akkoyun/B101/Output/2026-02-18/Schematic Print/Schematic Prints.PDF

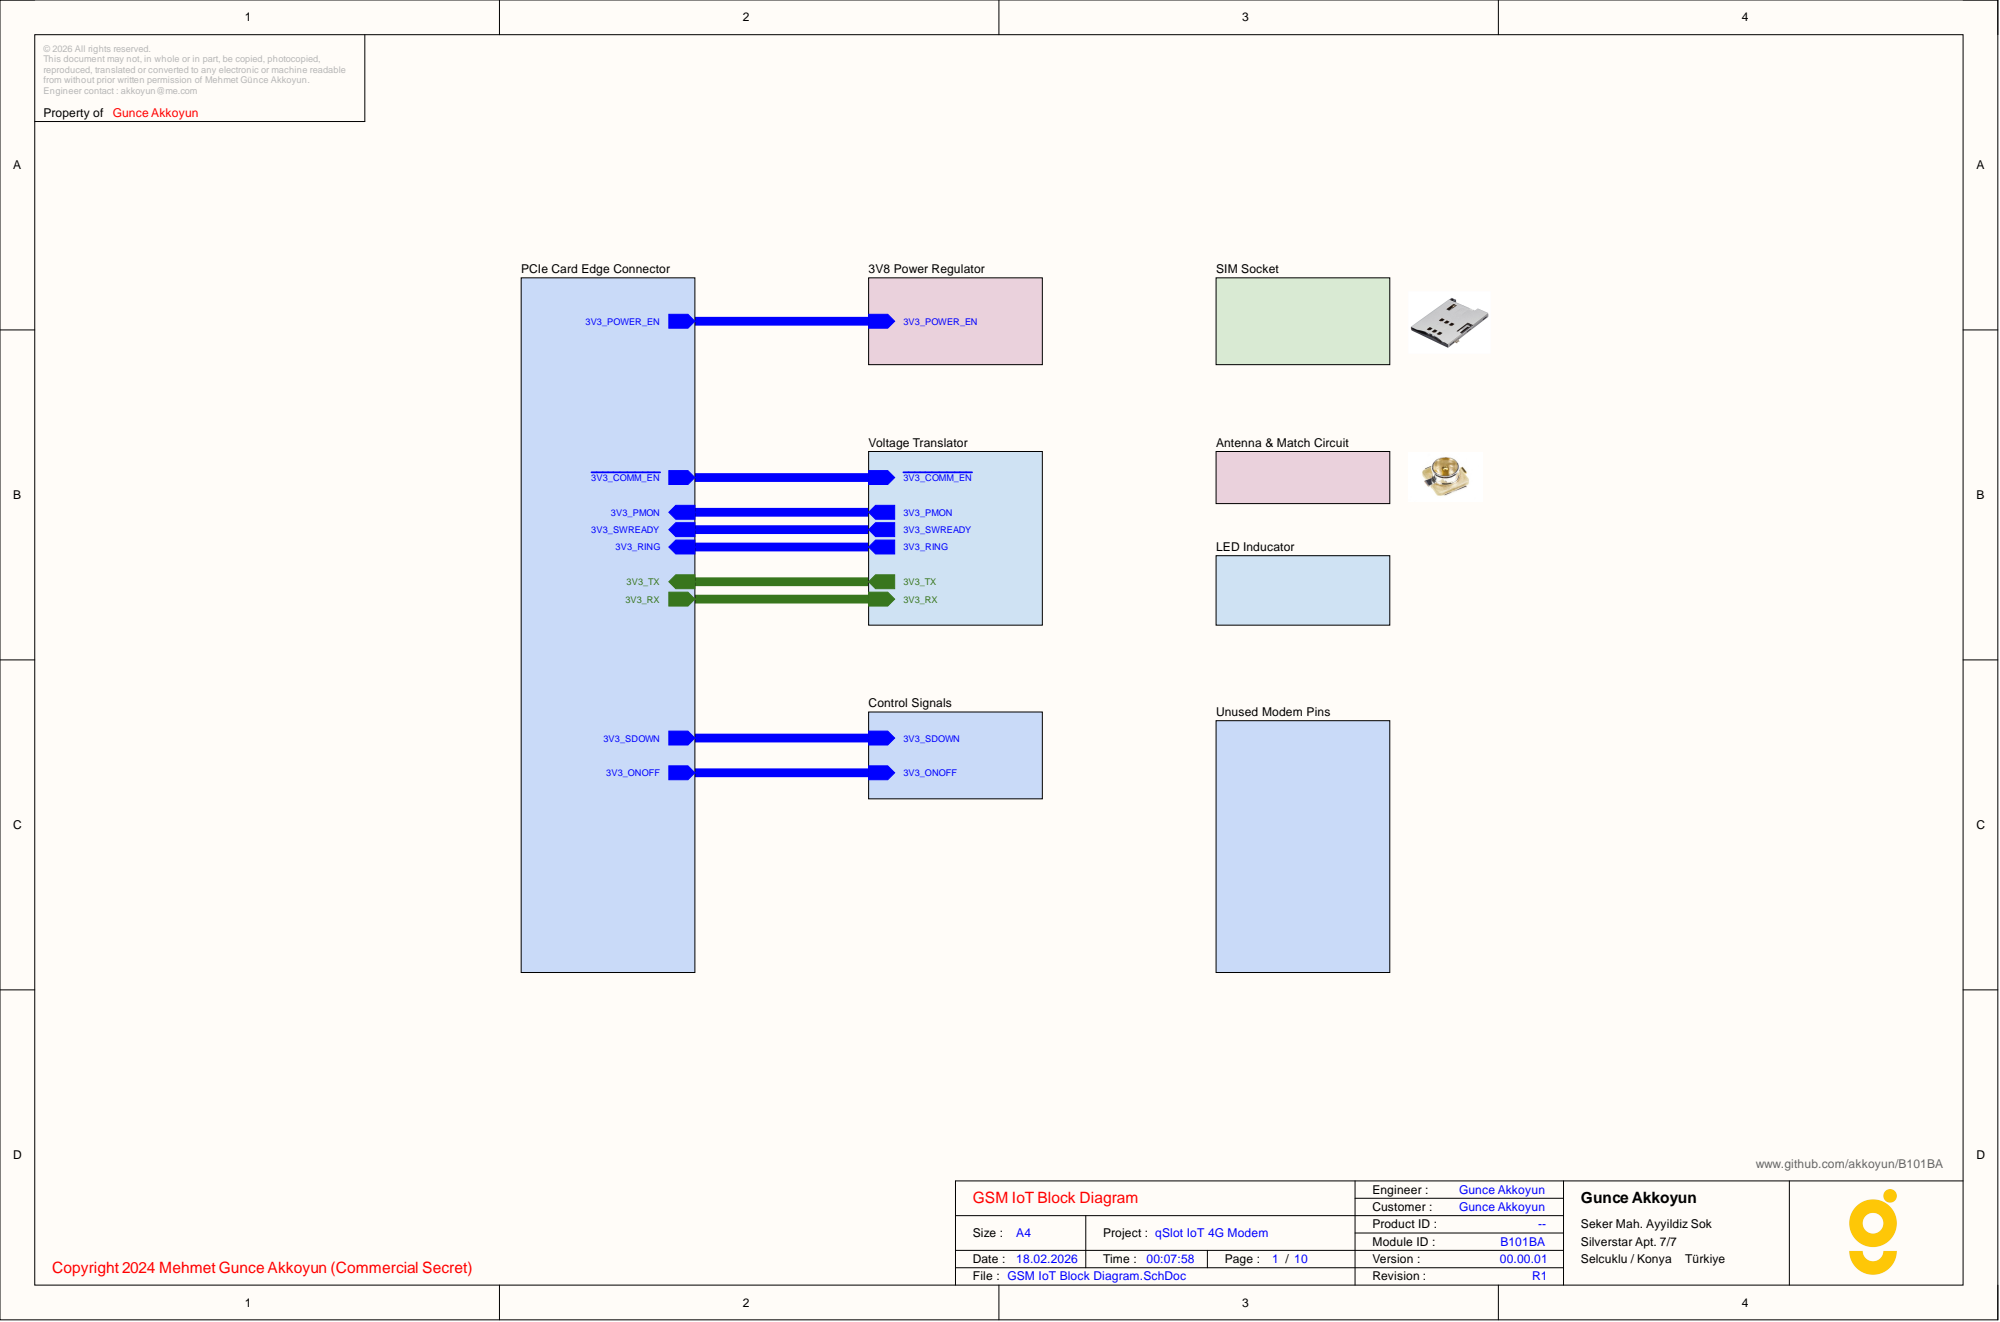
[picture p13: page 1]

© 2026 All rights reserved.
This document may not, in whole or in part, be copied, photocopied,
reproduced, translated or converted to any electronic or machine readable
from without prior written permission of Mehmet Günce Akkoyun.
Engineer contact : akkoyun@me.com

Property of Gunce Akkoyun

PCIe Card Edge Connector

www.github.com/akkoyun/B101BA

GSM IoT Block Diagram

Seker Mah. Ayyildiz Sok
Silverstar Apt. 7/7
Selcuklu / Konya Türkiye

Copyright 2024 Mehmet Gunce Akkoyun (Commercial Secret)

File : GSM IoT Block Diagram.SchDoc

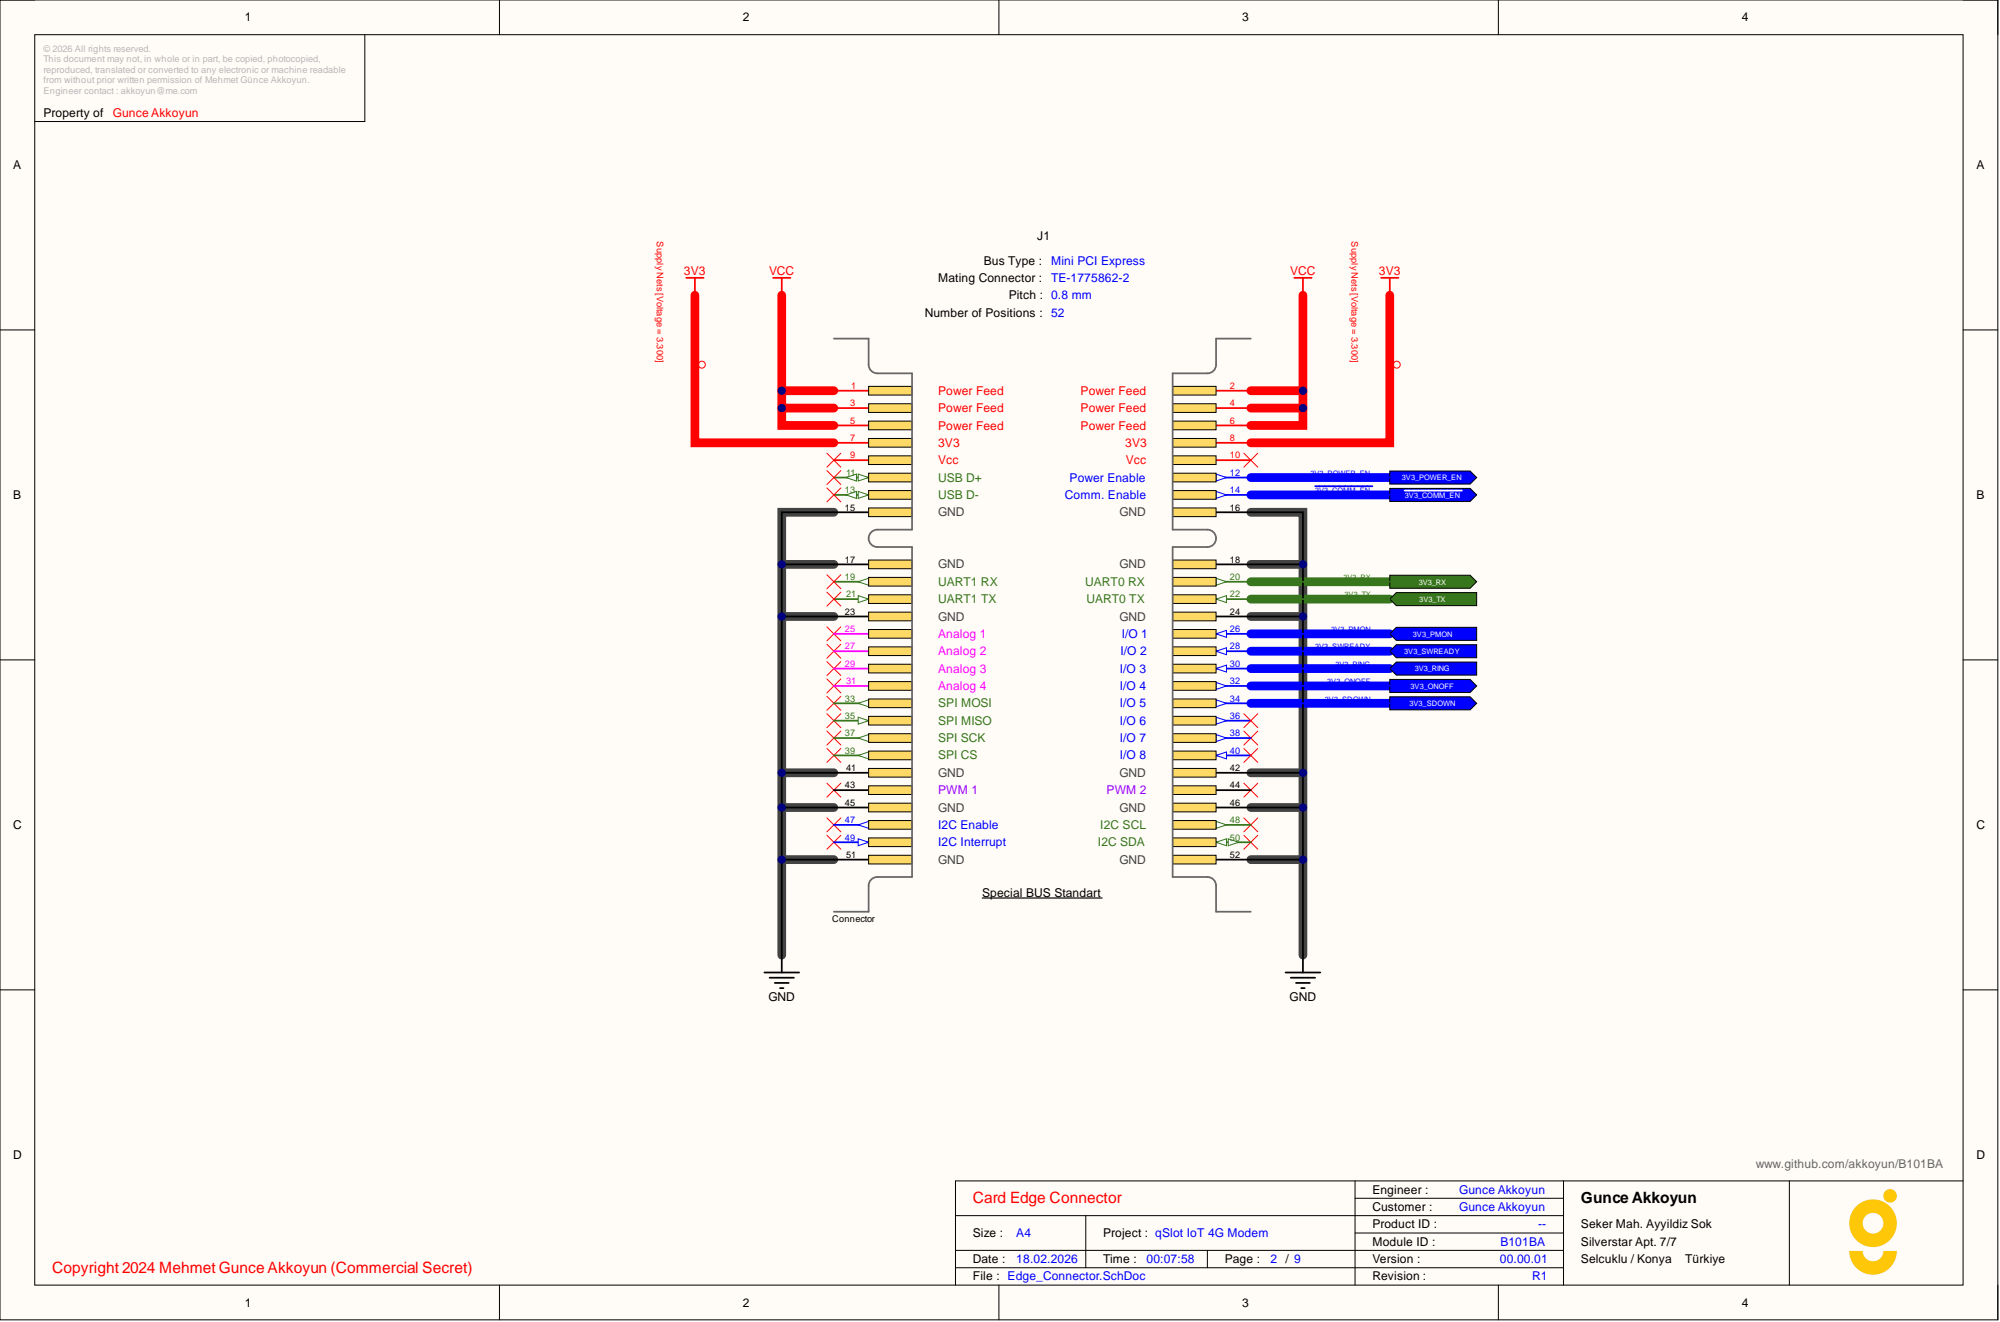
[picture p14: page 2]

Property of Gunce Akkoyun

www.github.com/akkoyun/B101BA

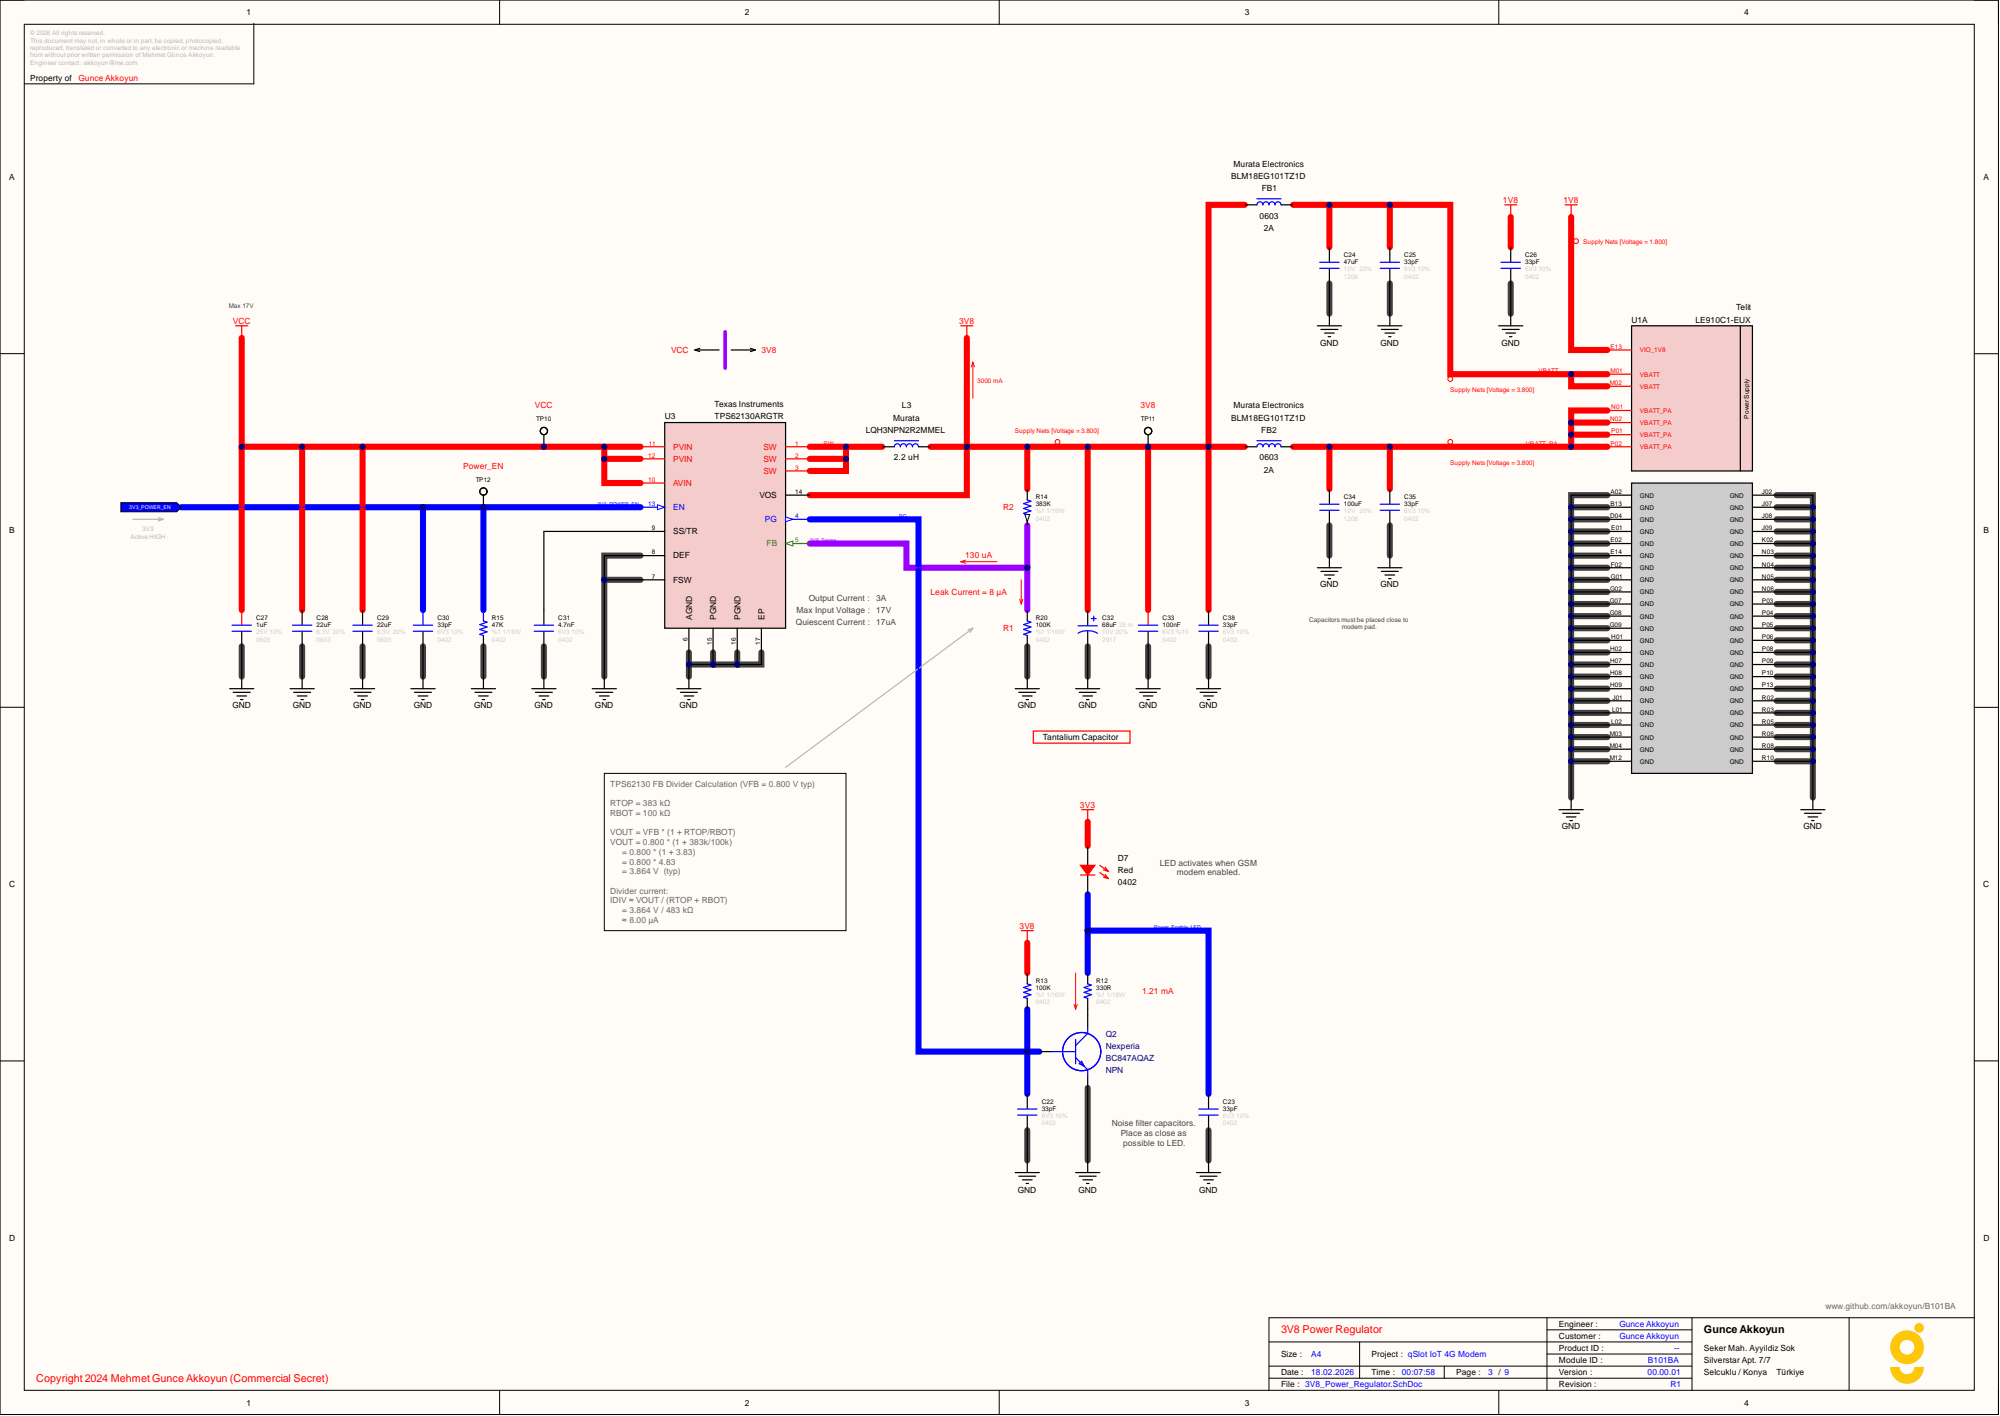
[picture p15: page 3]

Property of Gunce Akkoyun

Capacitors must be placed close to

TPS62130 FB Divider Calculation (VFB = 0.800 V typ)

Divider current:
IDIV ≈ VOUT / (RTOP + RBOT)

Noise filter capacitors.
Place as close as
possible to LED.

www.github.com/akkoyun/B101BA

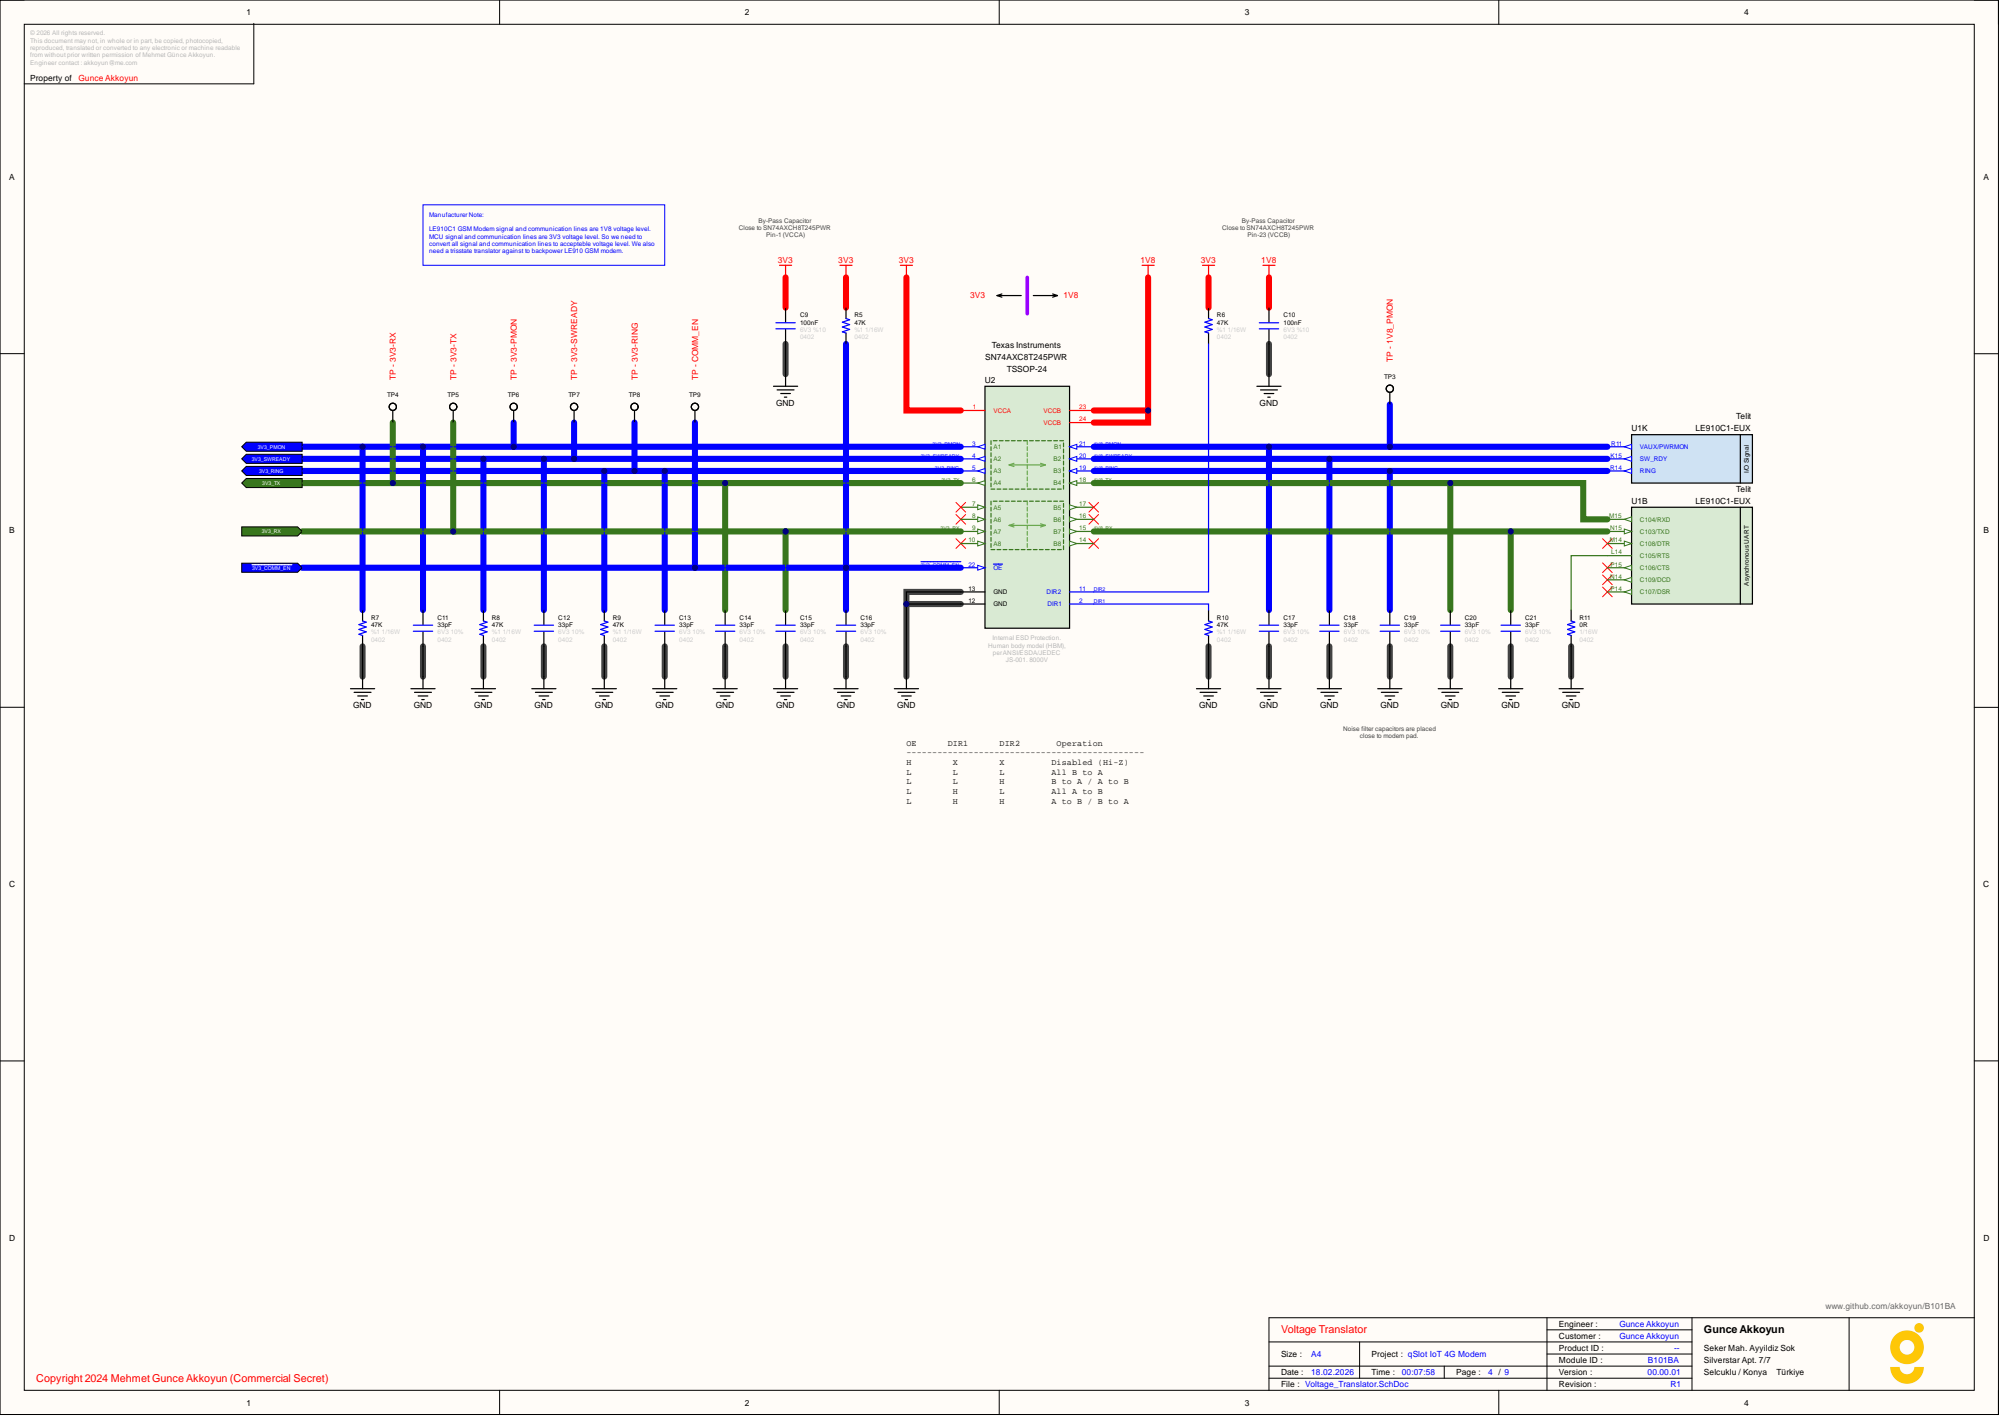
[picture p16: page 4]

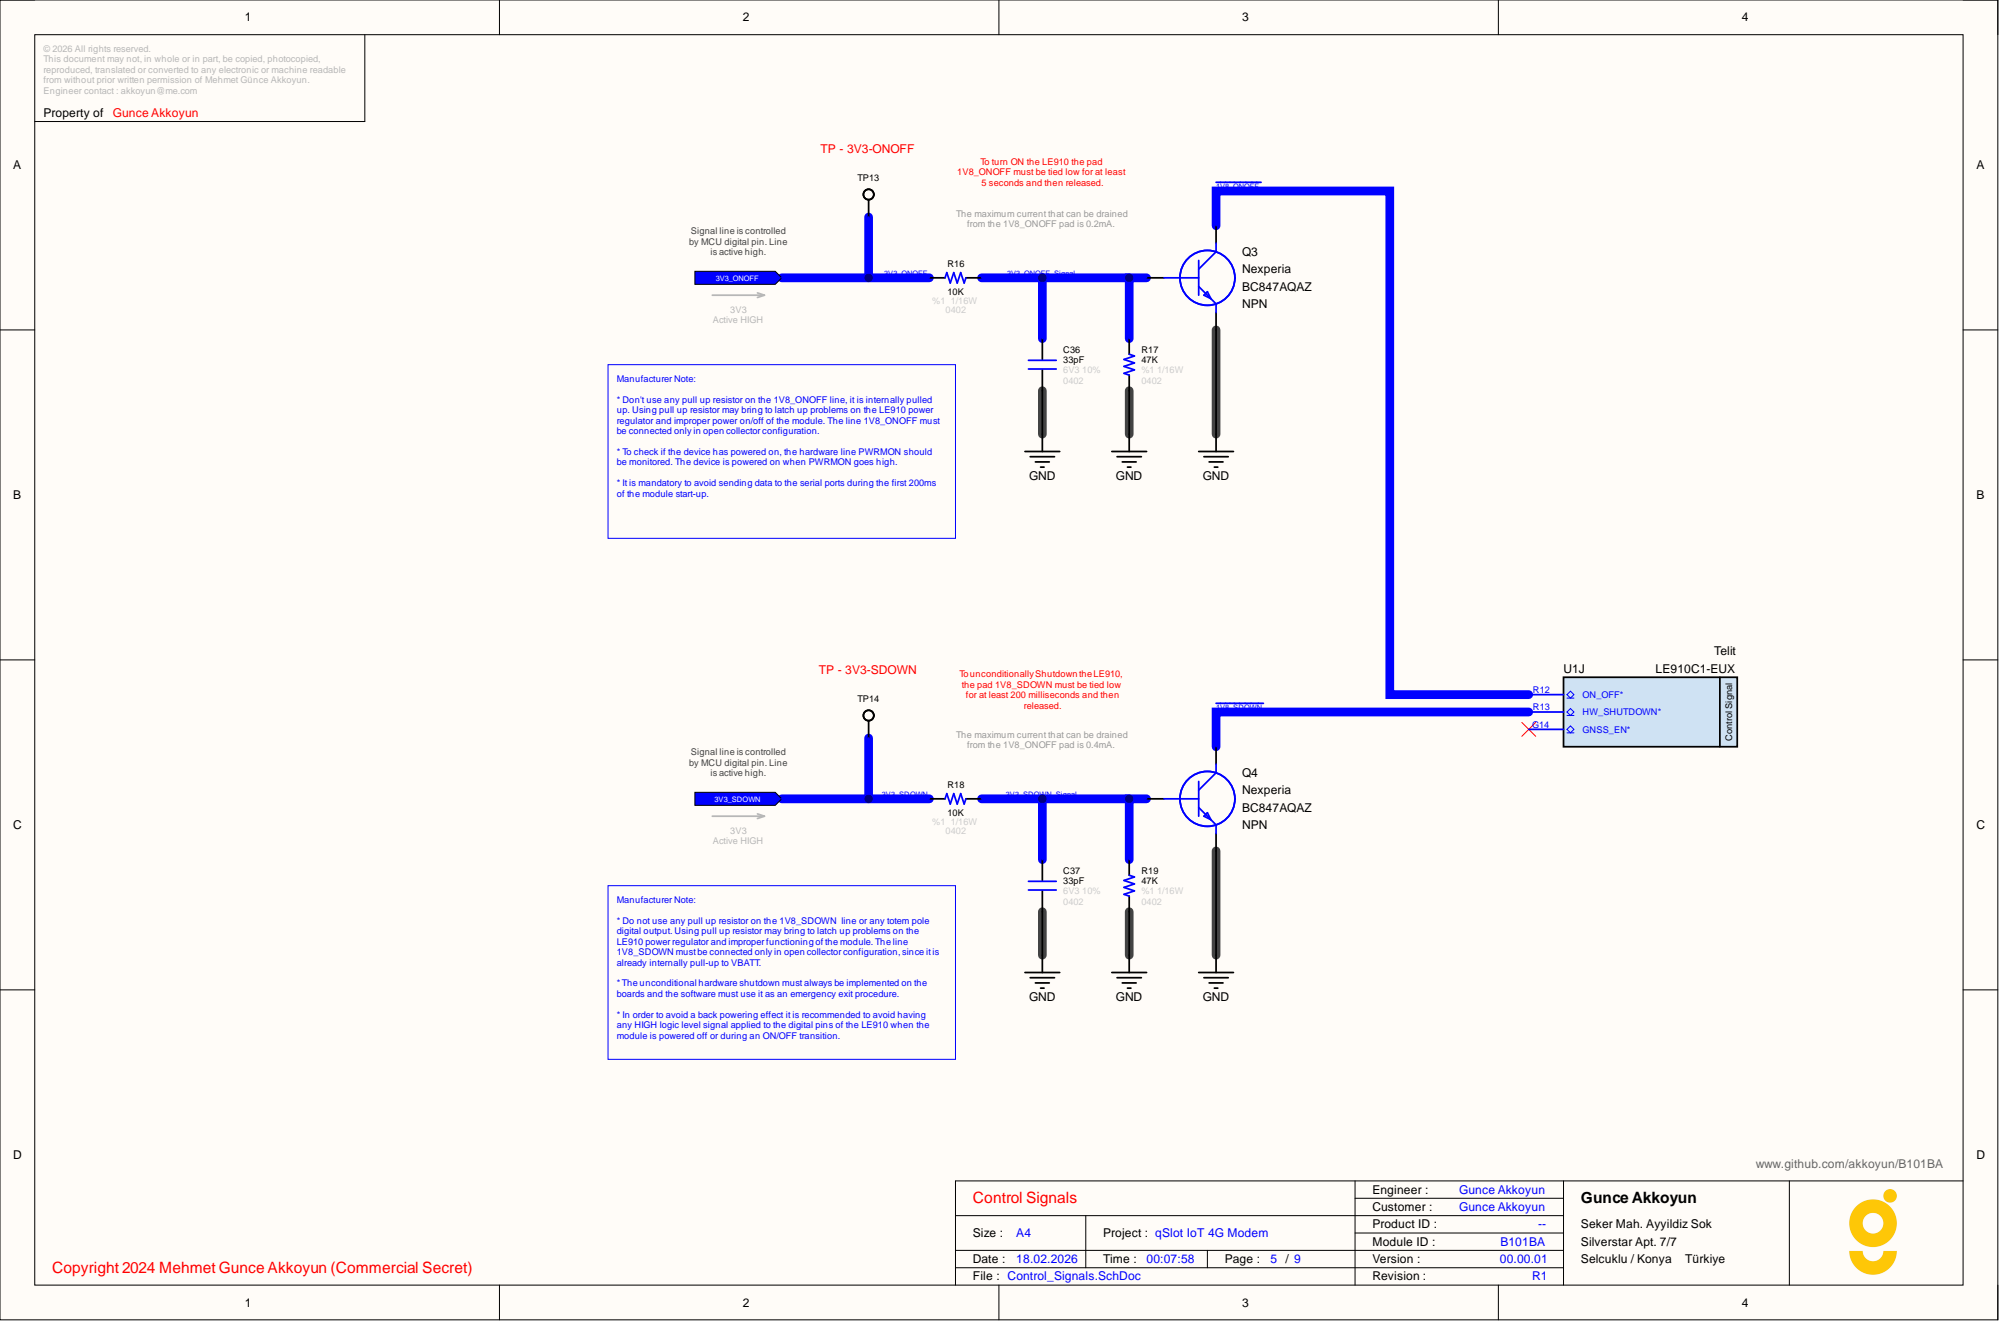
[picture p17: page 5]

Property of Gunce Akkoyun

To turn ON the LE910 the pad
1V8_ONOFF must be tied low for at least
5 seconds and then released.

The maximum current that can be drained
from the 1V8_ONOFF pad is 0.2mA.

Signal line is controlled
by MCU digital pin. Line
is active high.

* Don't use any pull up resistor on the 1V8_ONOFF line, it is internally pulled
up. Using pull up resistor may bring to latch up problems on the LE910 power
regulator and improper power on/off of the module. The line 1V8_ONOFF must
be connected only in open collector configuration.

* To check if the device has powered on, the hardware line PWRMON should
be monitored. The device is powered on when PWRMON goes high.

* It is mandatory to avoid sending data to the serial ports during the first 200ms
of the module start-up.

To unconditionally Shutdown the LE910,
the pad 1V8_SDOWN must be tied low
for at least 200 milliseconds and then

from the 1V8_ONOFF pad is 0.4mA.

* Do not use any pull up resistor on the 1V8_SDOWN line or any totem pole
digital output. Using pull up resistor may bring to latch up problems on the
LE910 power regulator and improper functioning of the module. The line
1V8_SDOWN must be connected only in open collector configuration, since it is
already internally pull-up to VBATT.

* The unconditional hardware shutdown must always be implemented on the
boards and the software must use it as an emergency exit procedure.

* In order to avoid a back powering effect it is recommended to avoid having
any HIGH logic level signal applied to the digital pins of the LE910 when the
module is powered off or during an ON/OFF transition.

www.github.com/akkoyun/B101BA

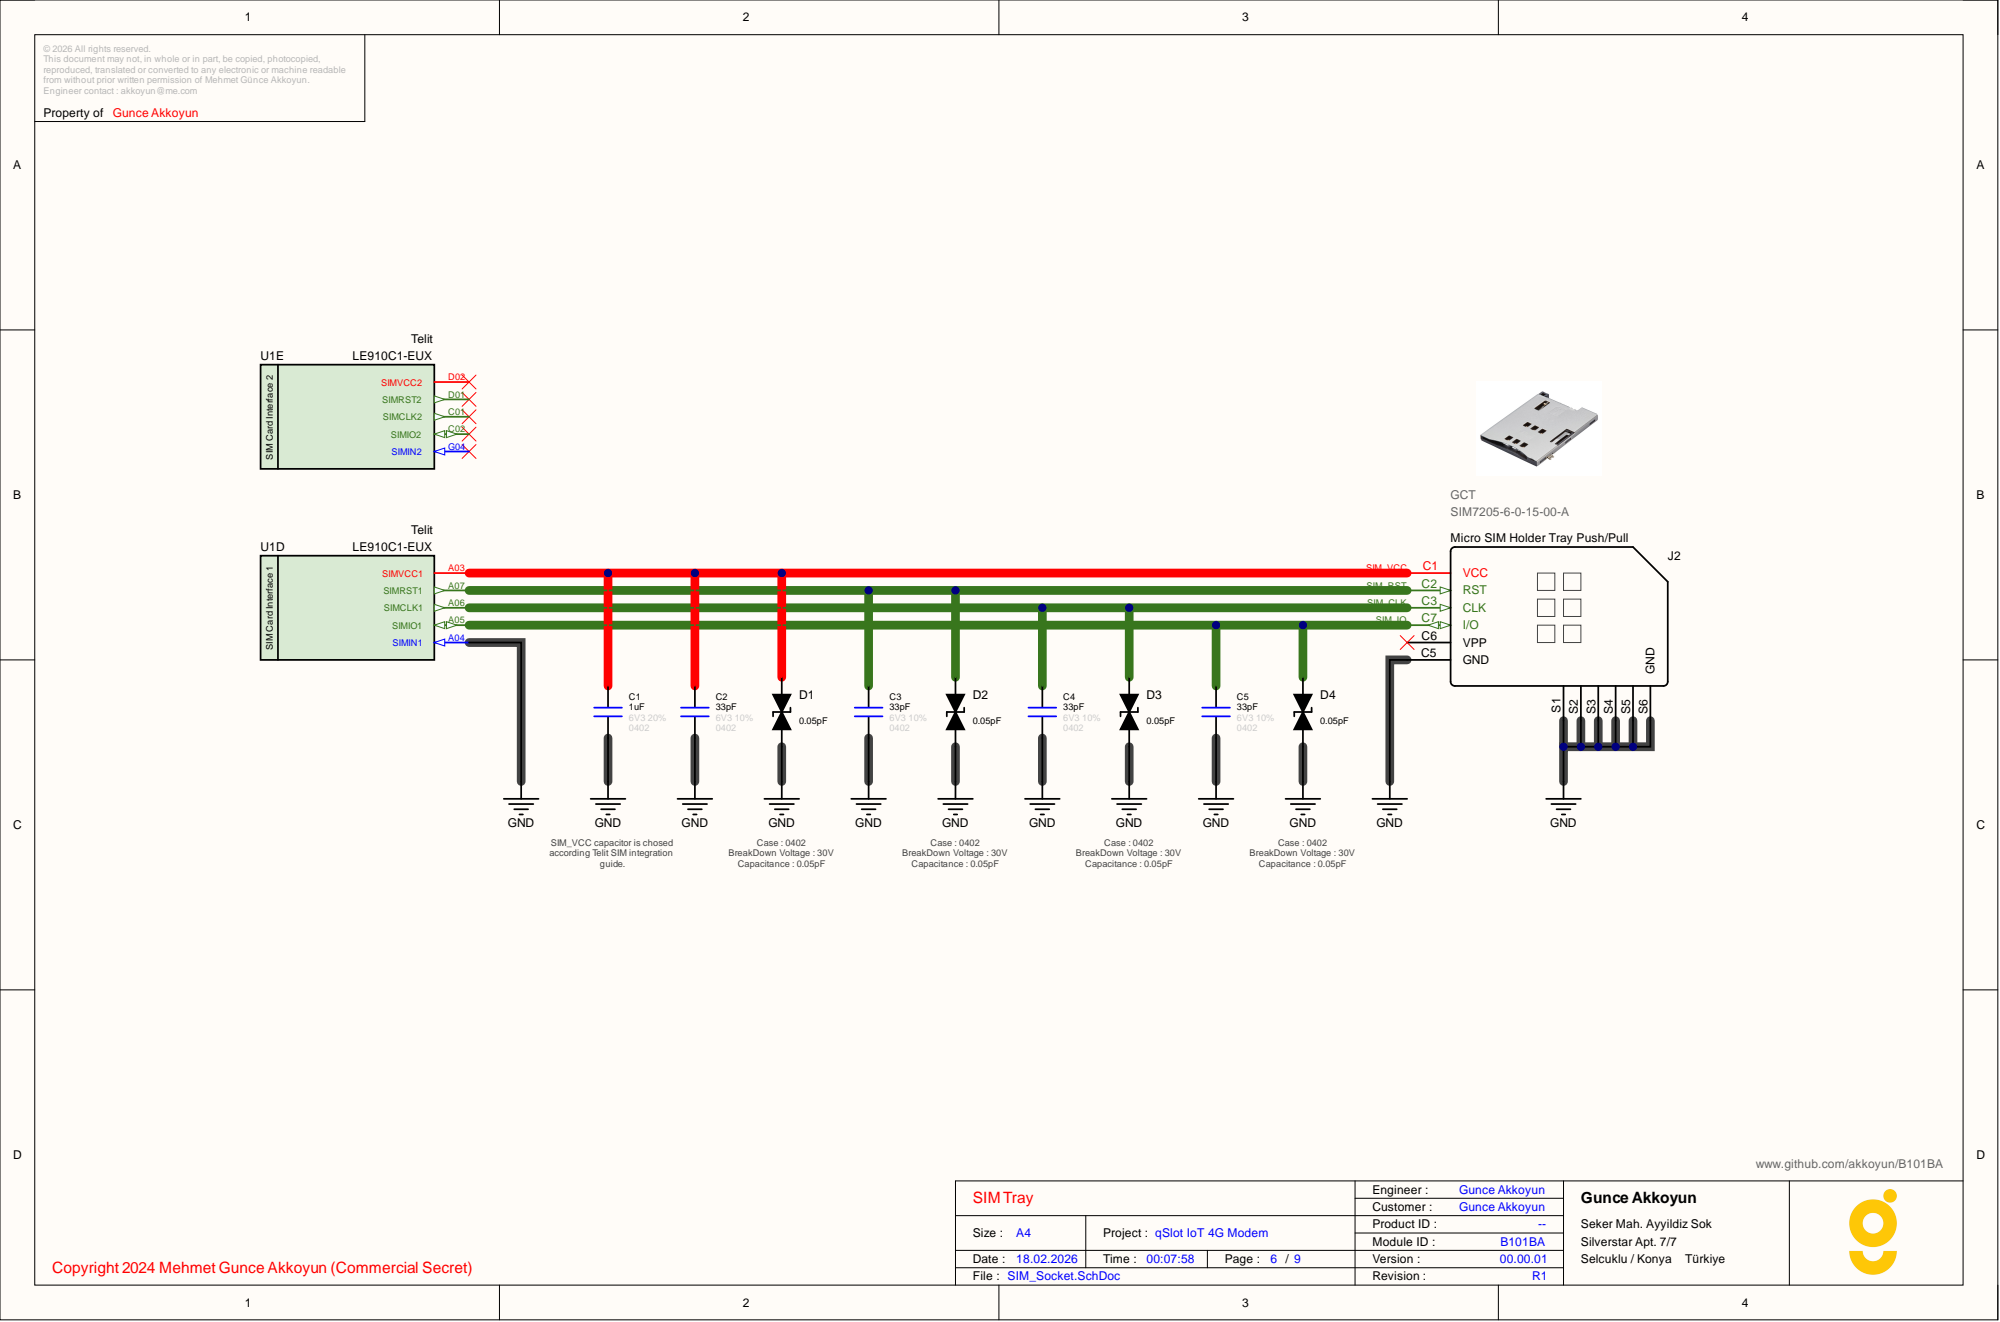
[picture p18: page 6]

A05 | | M_CLK SIM_IO

A04 | | | VPP C6

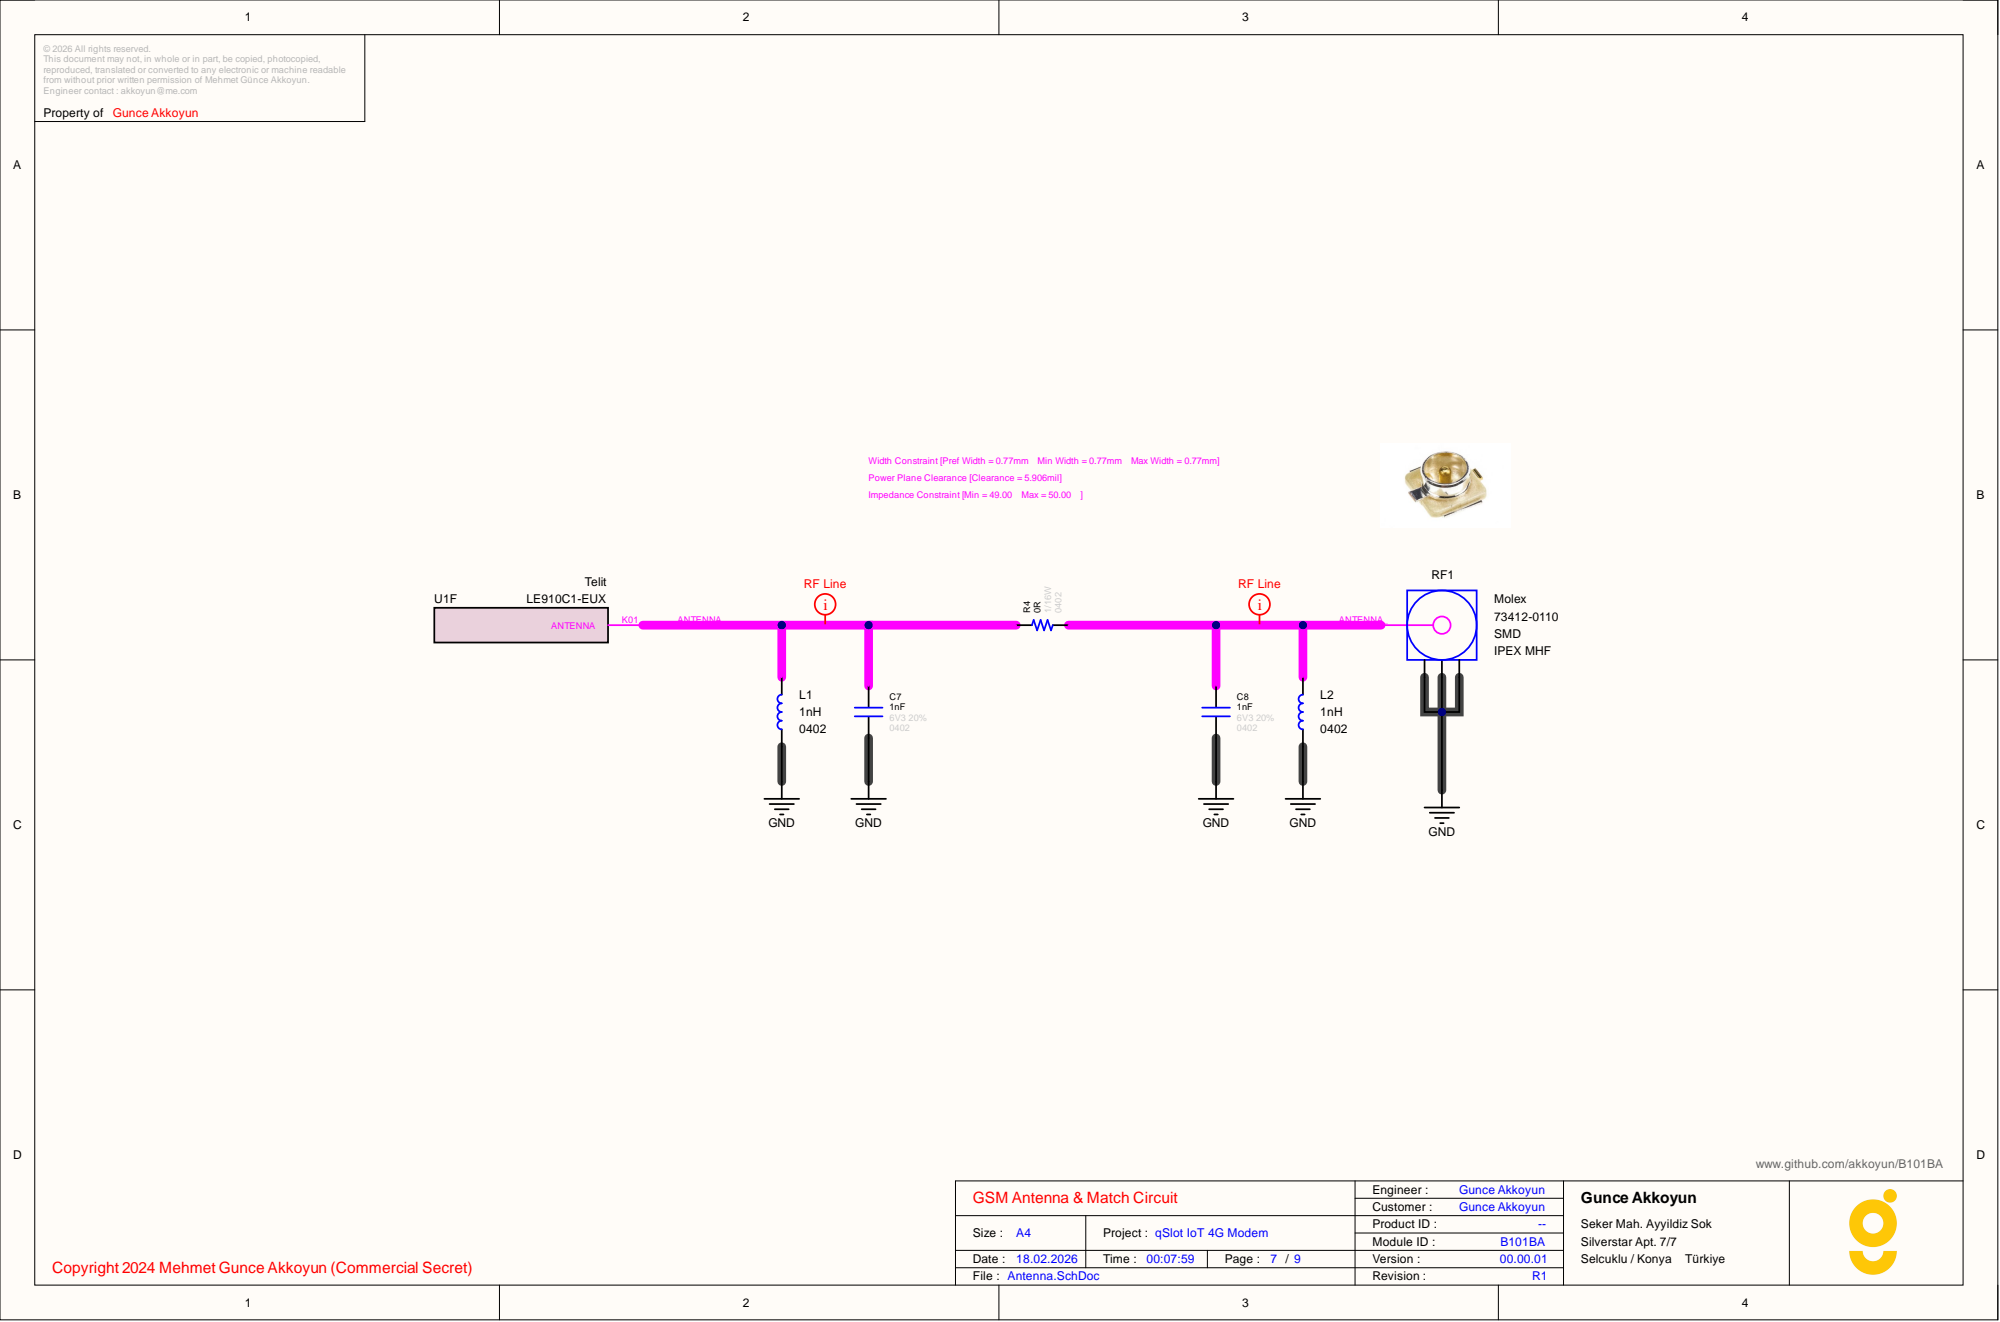
[picture p19: page 7]

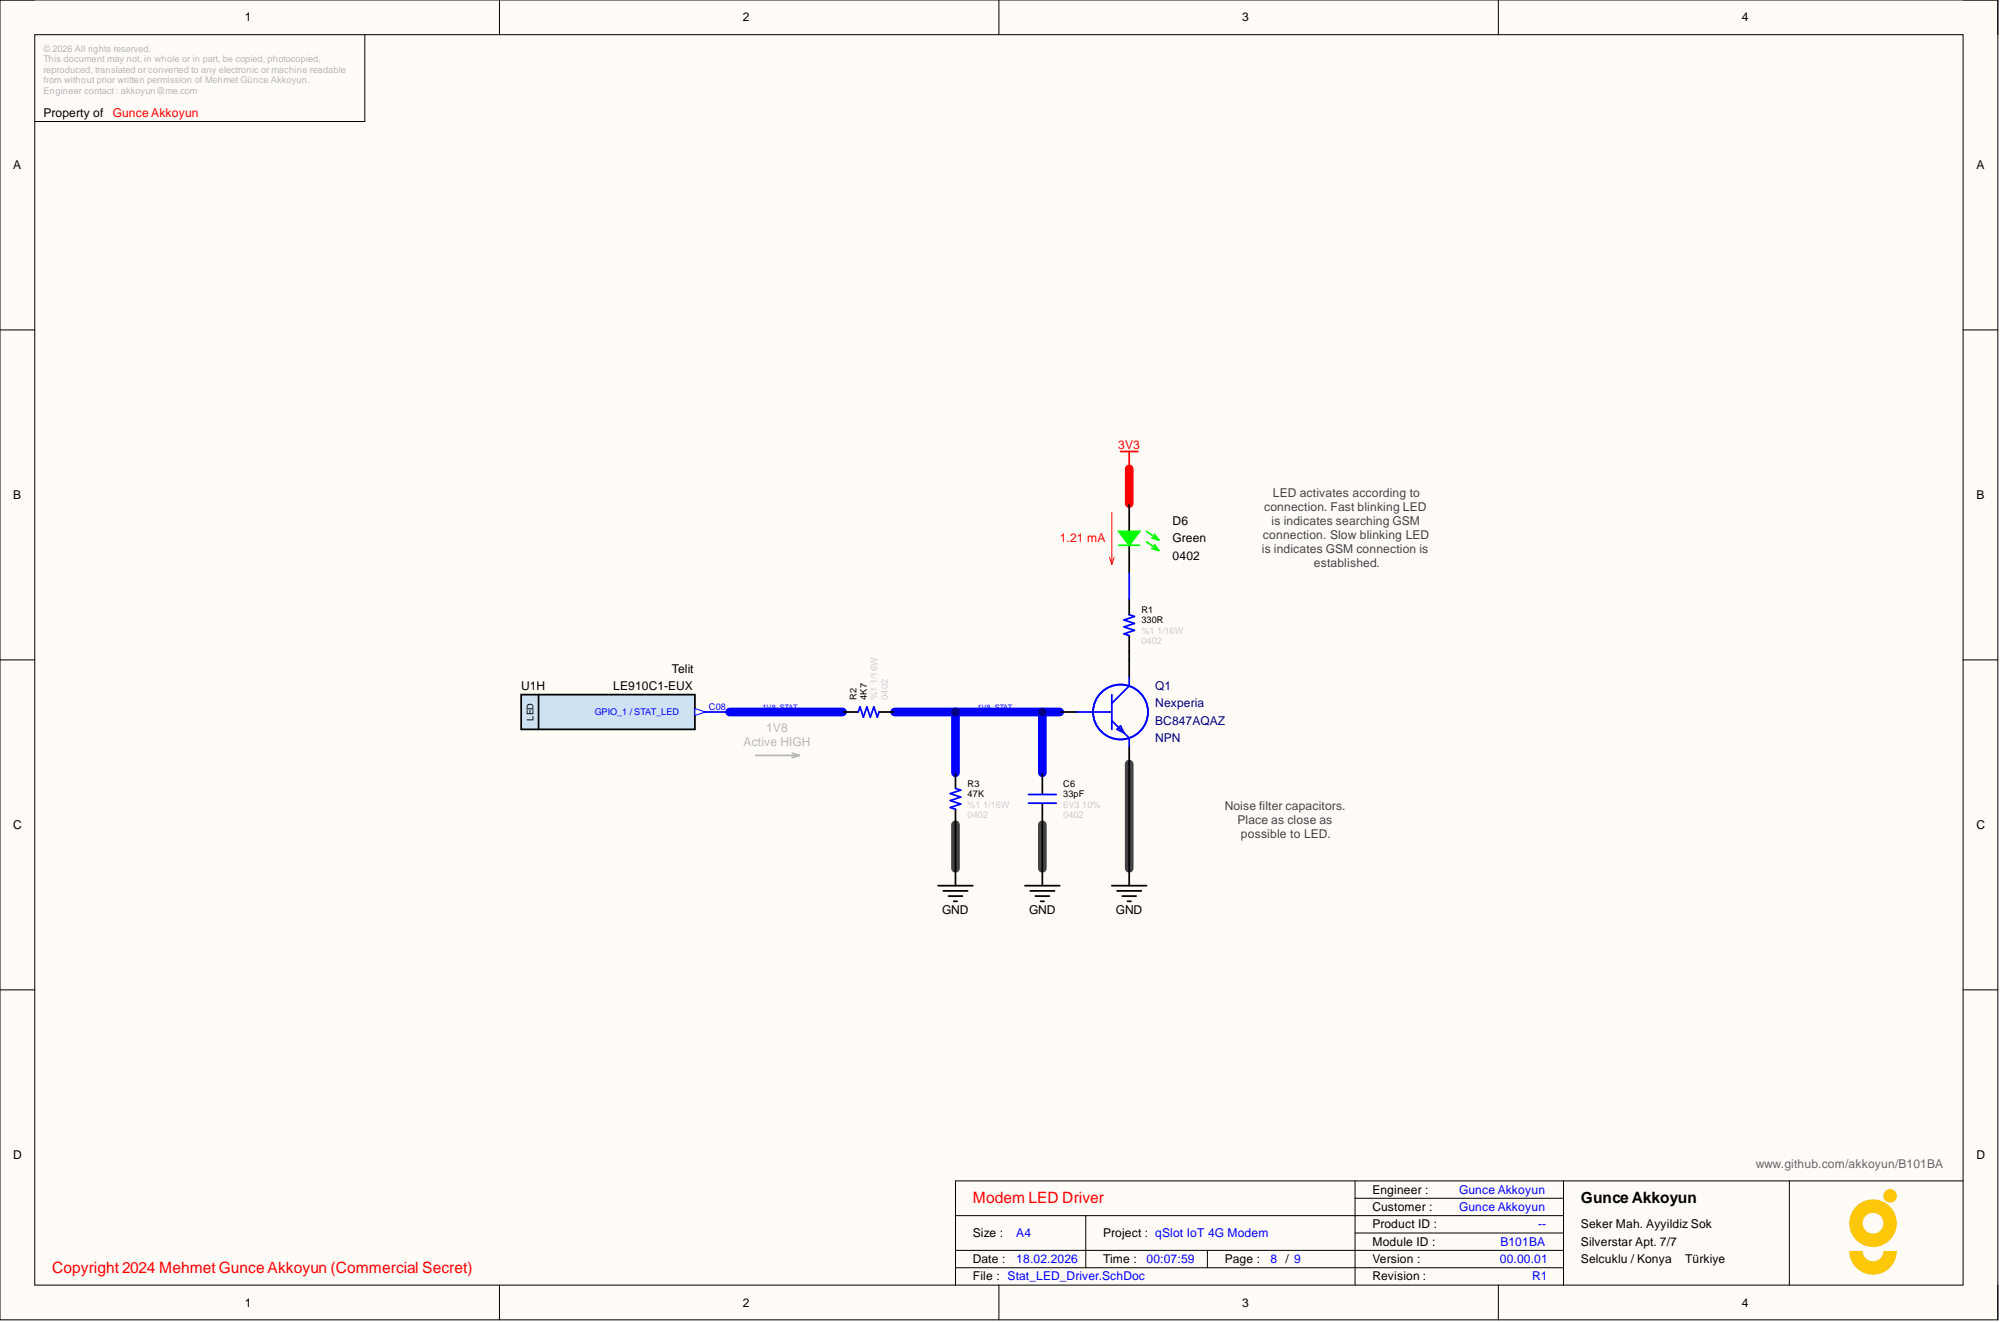
[picture p20: page 8]

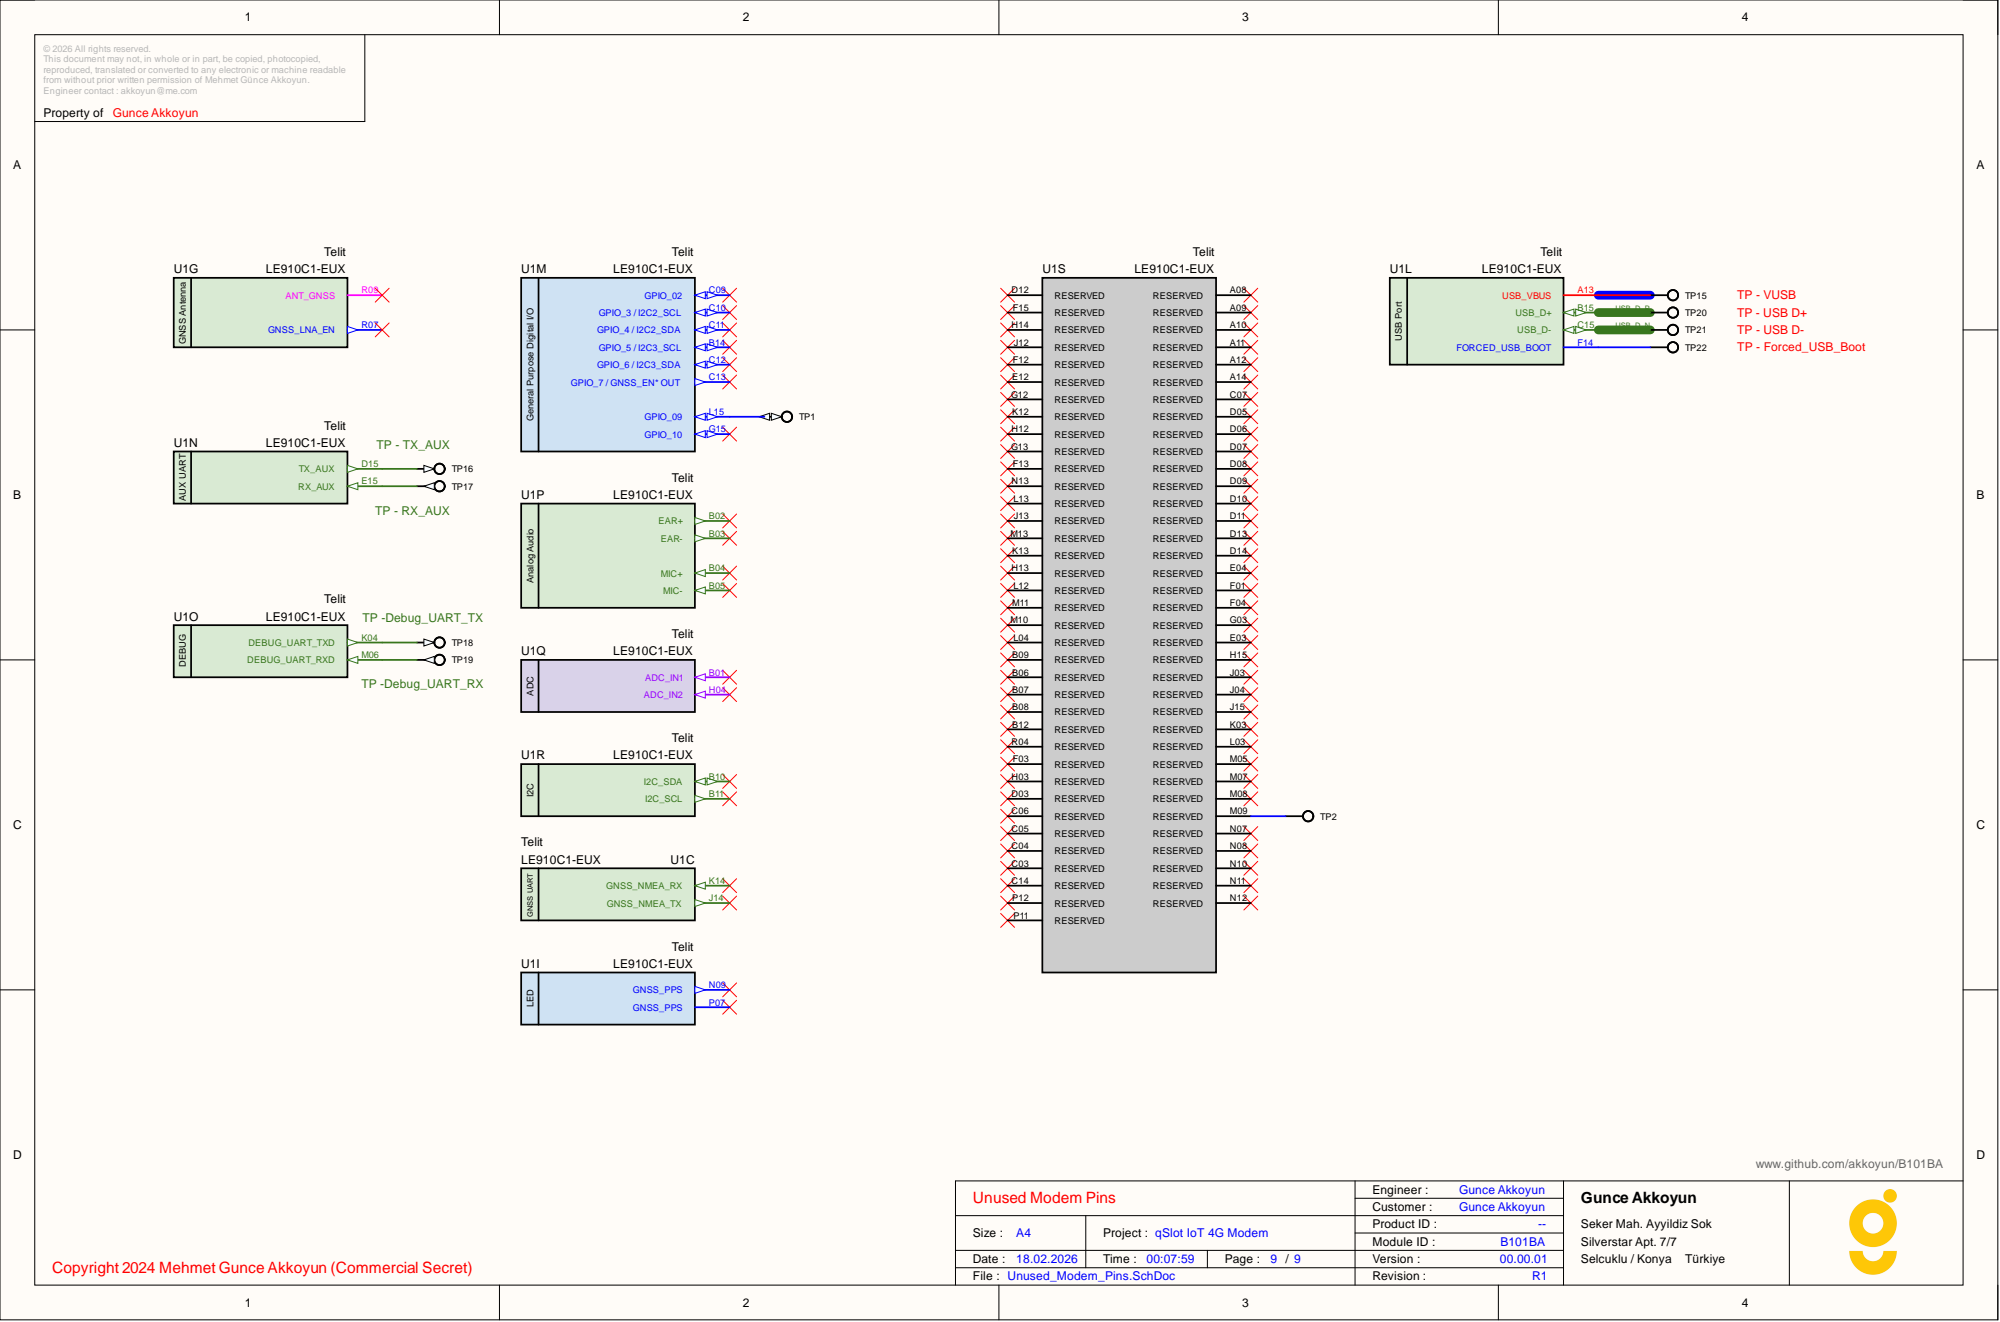
[picture p21: page 9]

TX_A U X R X_A U X | 0C1-EUX Telit U1 P LE9 1
