akkoyun/B101/Output/2026-02-18/PCB 3D Print/B101BA.png

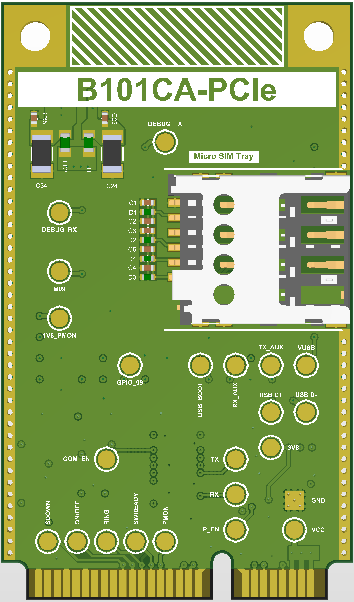
Output/2026-02-18/PCB 3D Print/B101BA.png
