akkoyun/B101/Output/2026-04-23/PCB 3D Print/B101BA(Production).png

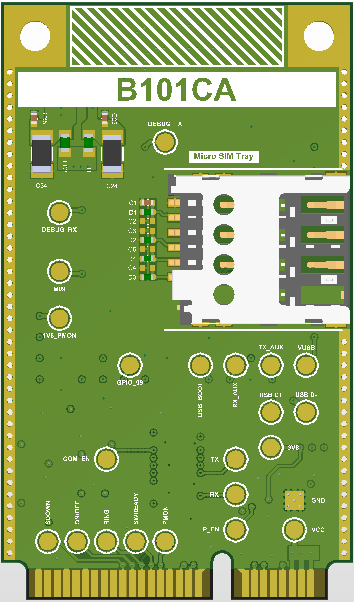
Output/2026-04-23/PCB 3D Print/B101BA(Production).png
