akkoyun/B101/Output/2026-02-26/PCBDrawing/Draftsman.PDF

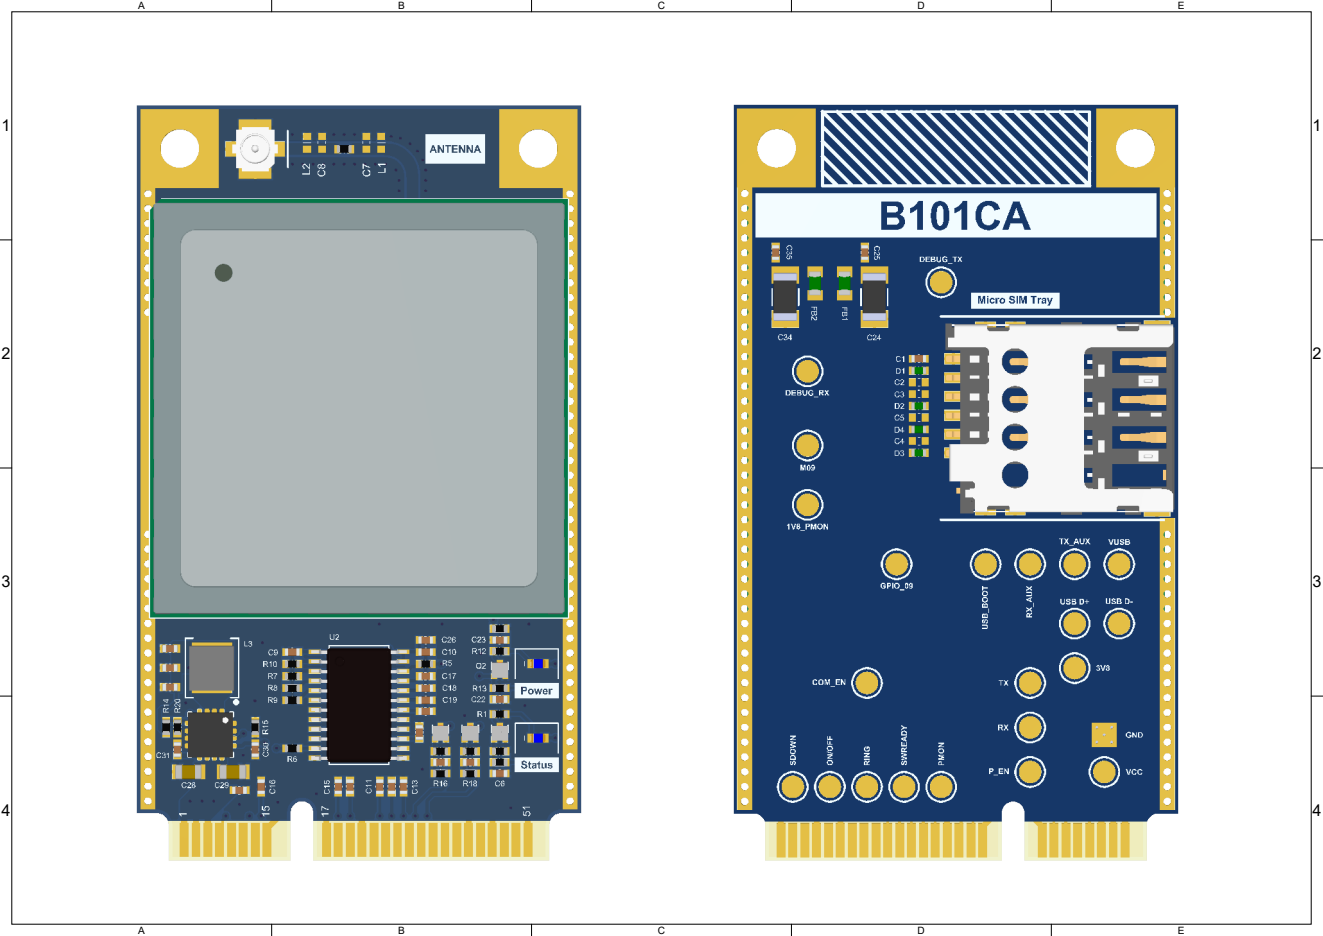
[picture p53: page 1]

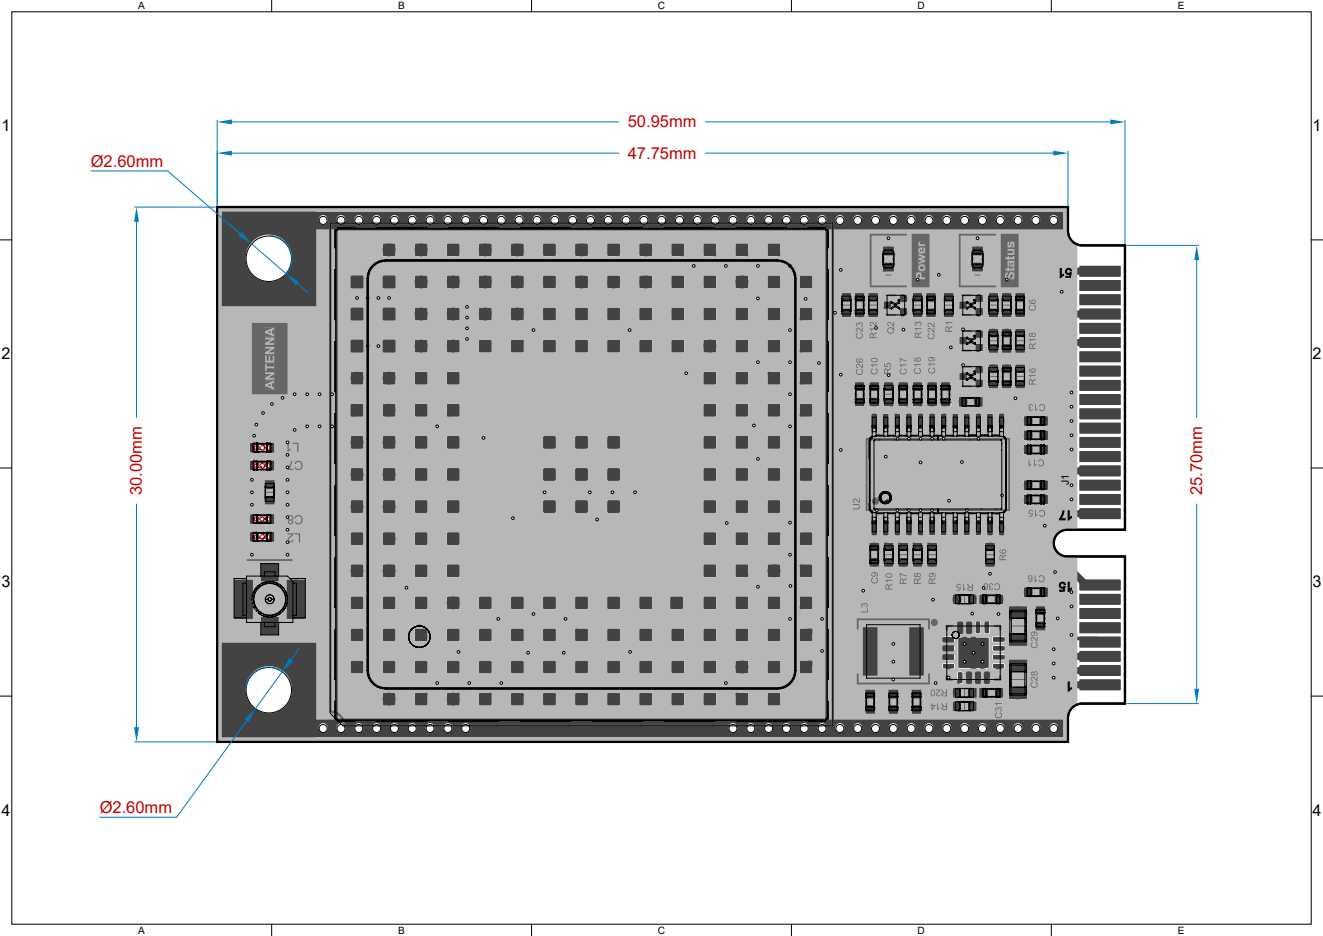
[picture p54: page 2]


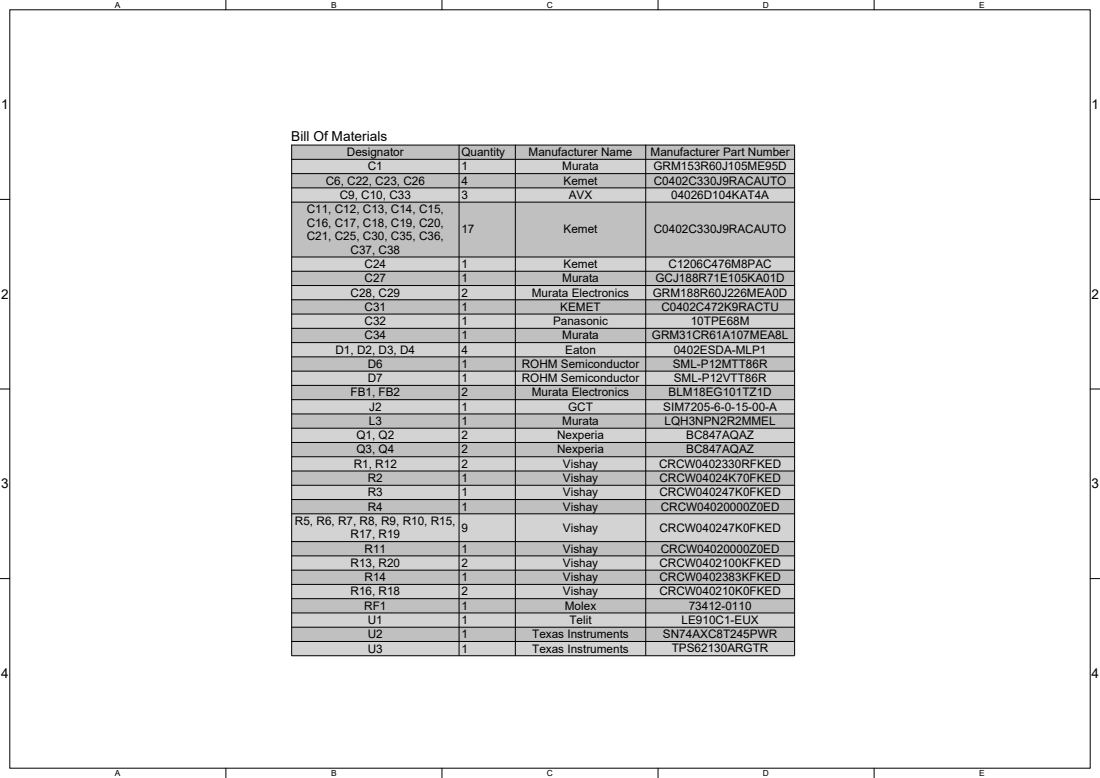
[picture p55: page 4]

Designator | | Manufacturer Name | Manufacturer Part Number
C1 | Quantity 143 | Murata | GRM153R60J105ME95D

C6, C22, C23, C26 | | Kemet | C0402C330J9RACAUTO
C9, C10, C33 | | AVX | 04026D104KAT4A
C11, C12, C13, C14, C15, C16, C17, C18, C19, C20, C21, C25, C30, C35, C36, C37, C38 | | Kemet | C0402C330J9RACAUTO

D6 | 17112111411211222111912121111 | ROHM Semiconductor | SML-P12MTT86R

C24 | | Kemet | C1206C476M8PAC
C27 | | Murata | GCJ188R71E105KA01D
C28, C29 | | Murata Electronics | GRM188R60J226MEA0D
C31 | | KEMET | C0402C472K9RACTU
C32 | | Panasonic | 10TPE68M
C34 | | Murata | GRM31CR61A107MEA8L
D1, D2, D3, D4 | | Eaton | 0402ESDA-MLP1

D7 | | ROHM Semiconductor | SML-P12VTT86R
FB1, FB2 | | Murata Electronics | BLM18EG101TZ1D
J2 | | GCT | SIM7205-6-0-15-00-A
L3 | | Murata | LQH3NPN2R2MMEL
Q1, Q2 | | Nexperia | BC847AQAZ
Q3, Q4 | | Nexperia | BC847AQAZ
R1, R12 | | Vishay | CRCW0402330RFKED
R2 | | Vishay | CRCW04024K70FKED
R3 | | Vishay | CRCW040247K0FKED
R4 | | Vishay | CRCW04020000Z0ED

R5, R6, R7, R8, R9, R10, R15, R17, R19 | | Vishay | CRCW040247K0FKED

R11 | | Vishay | CRCW04020000Z0ED
R13, R20 | | Vishay | CRCW0402100KFKED
R14 | | Vishay | CRCW0402383KFKED
R16, R18 | | Vishay | CRCW040210K0FKED
RF1 | | Molex | 73412-0110
U1 | | Telit | LE910C1-EUX
U2 | | Texas Instruments | SN74AXC8T245PWR
U3 | | Texas Instruments | TPS62130ARGTR

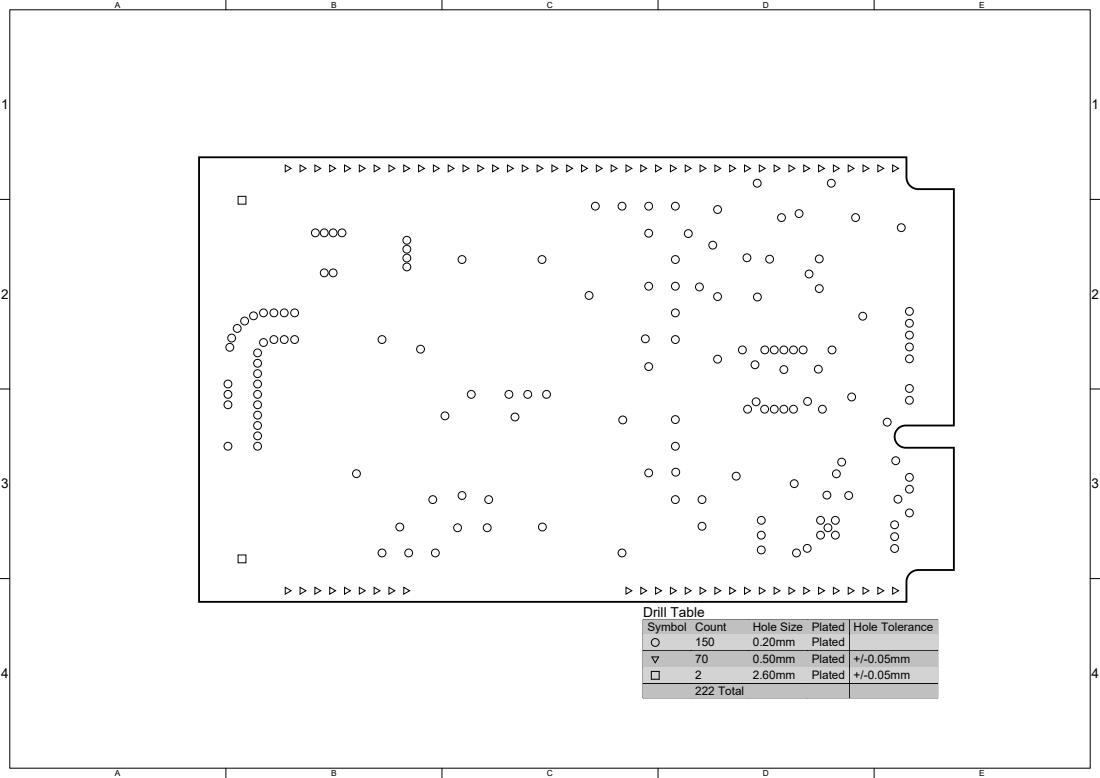
[picture p56: page 5]

Symbol | Count | Hole Size | Plated | Hole Tolerance

150 | 0.20mm | Plated
70 | 0.50mm | Plated | +/-0.05mm
2 | 2.60mm | Plated | +/-0.05mm
222 Total
