akkoyun/B101/Output/2026-04-28/PCB Print/Drill Drawing/Guides.PDF

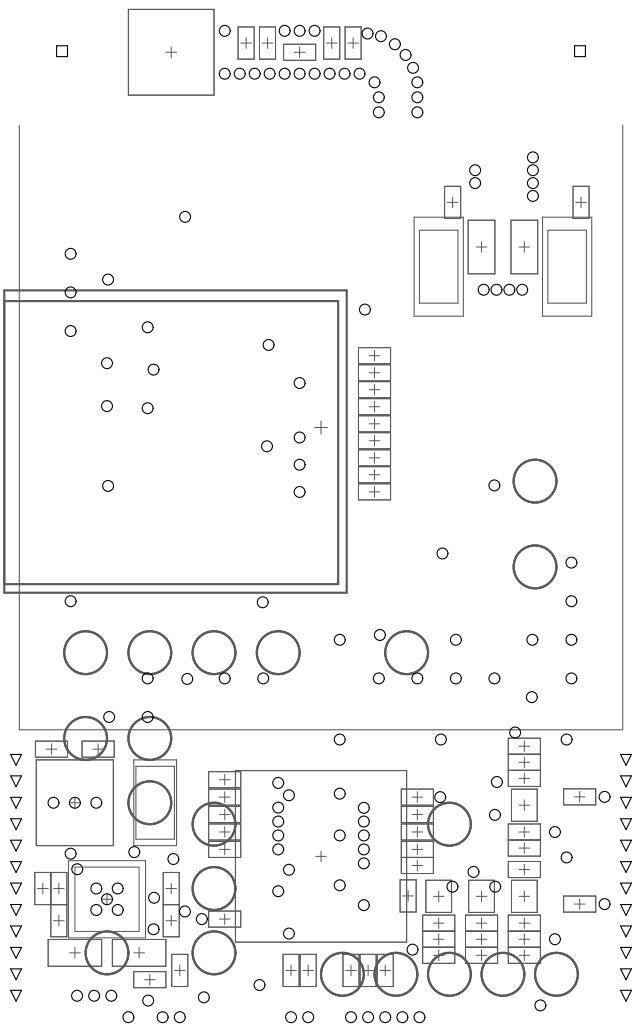
[picture p72: page 1]

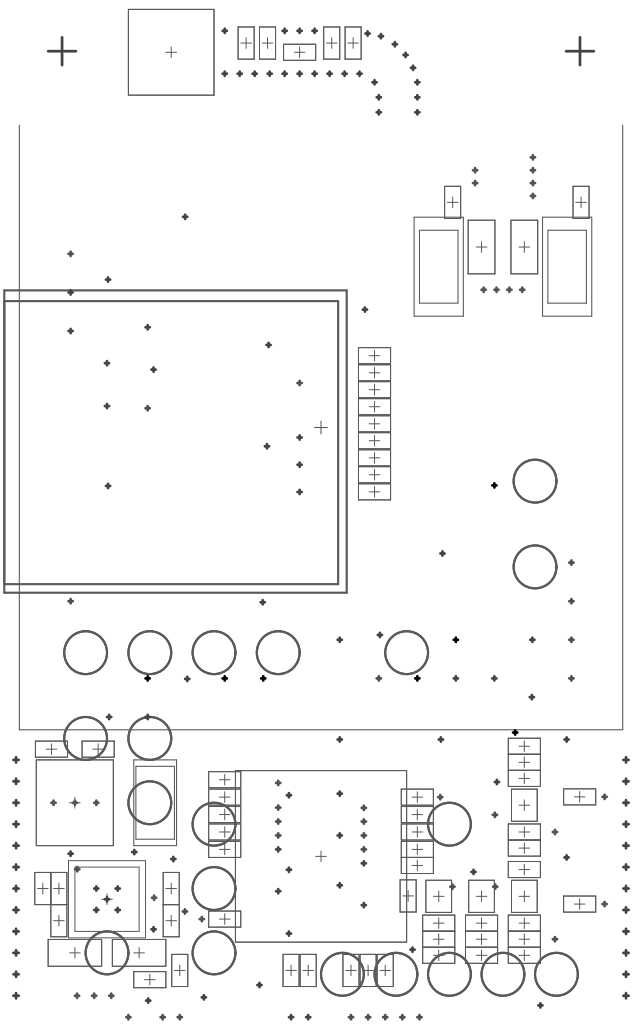
[picture p73: page 2]
