akkoyun/B101/Output/2026-04-28/PCB Print/Solder/Paste Mask Prints.PDF

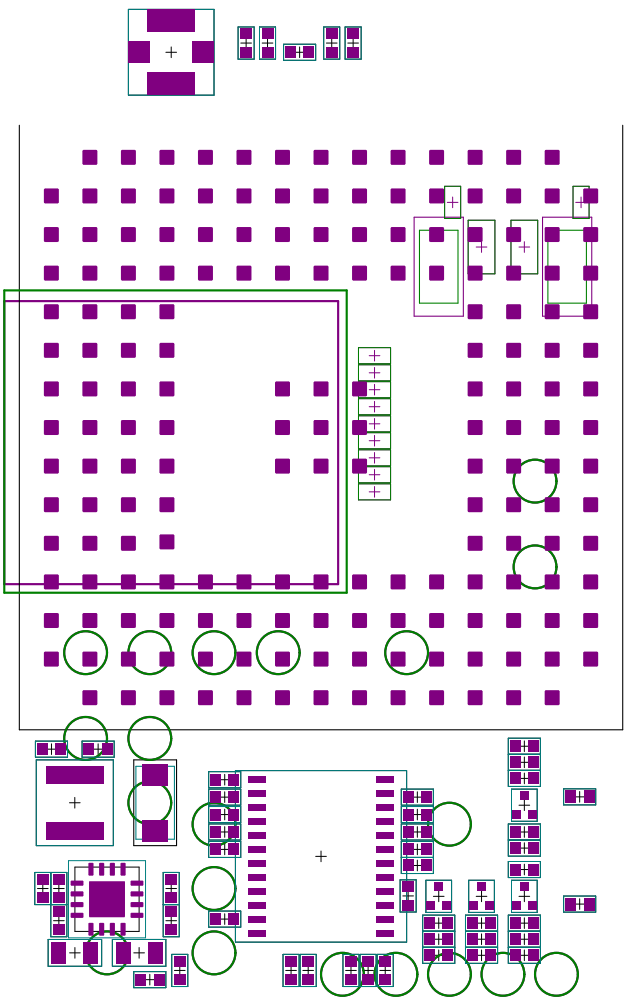
[picture p74: page 1]

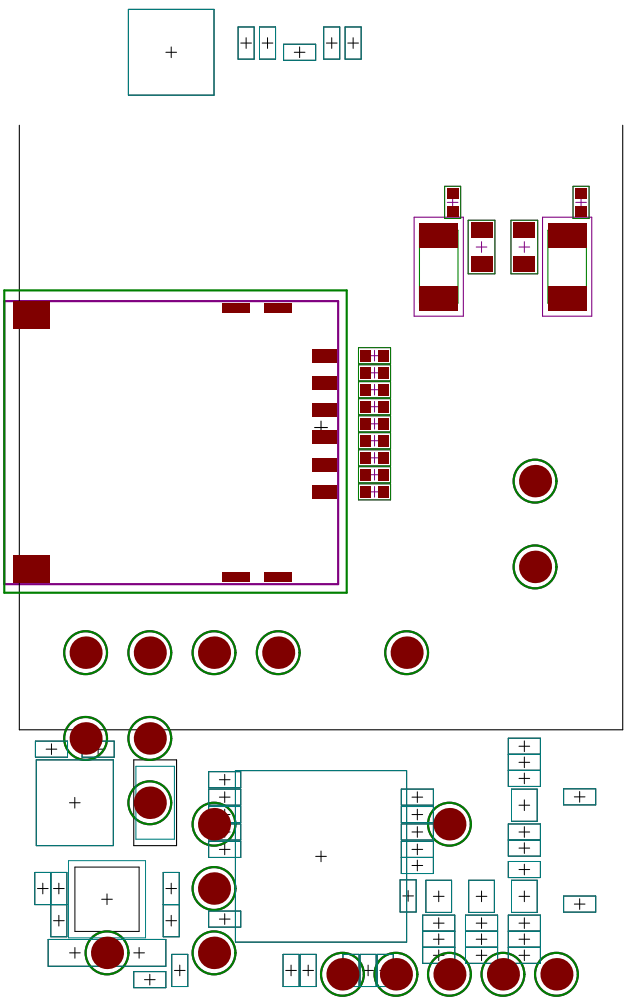
[picture p75: page 2]

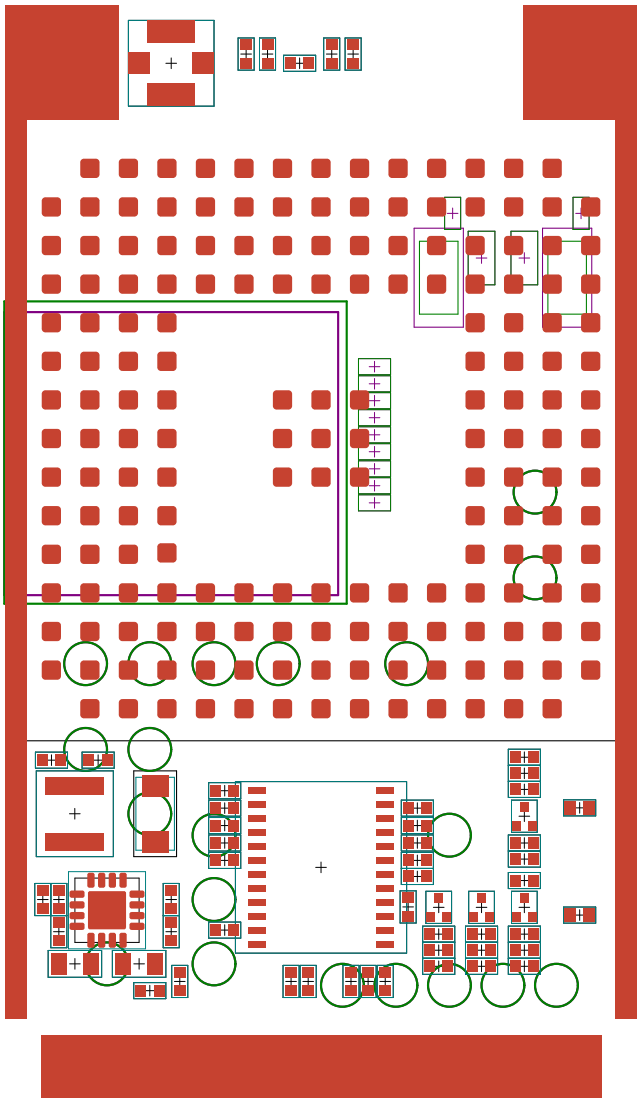
[picture p76: page 3]

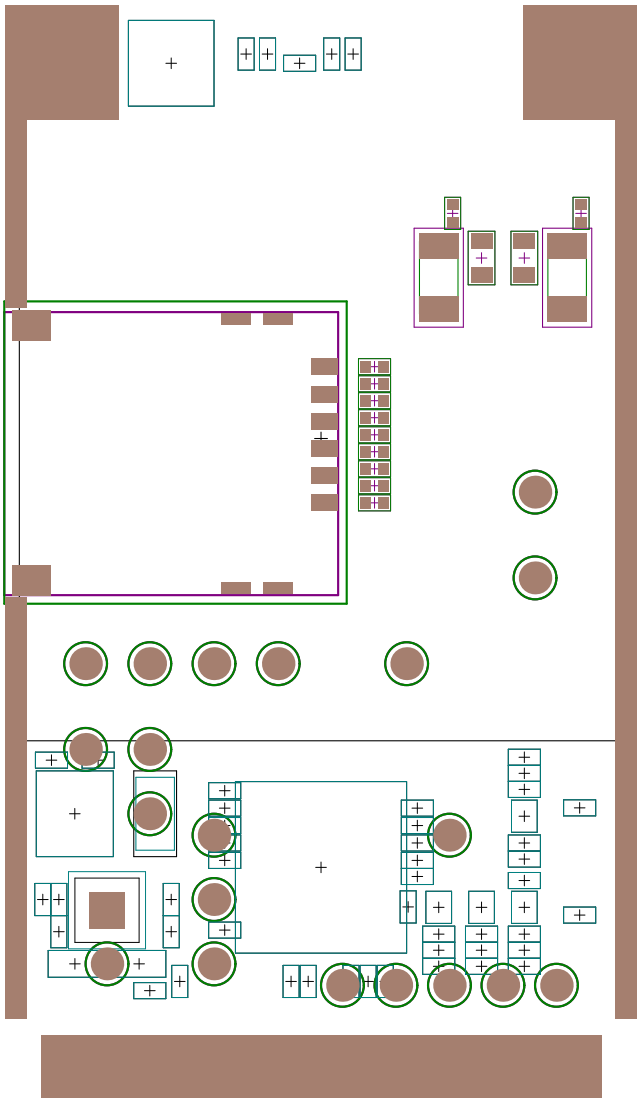
[picture p77: page 4]
