akkoyun/B101/Output/2026-04-23/PCB Print/Drill Drawing/Guides.PDF

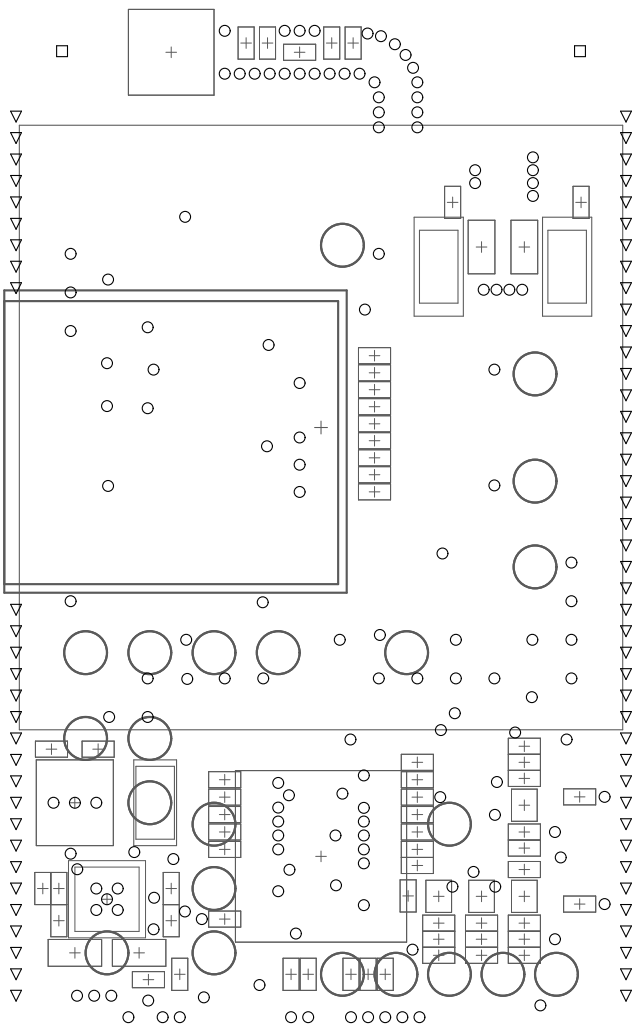
[picture p78: page 1]

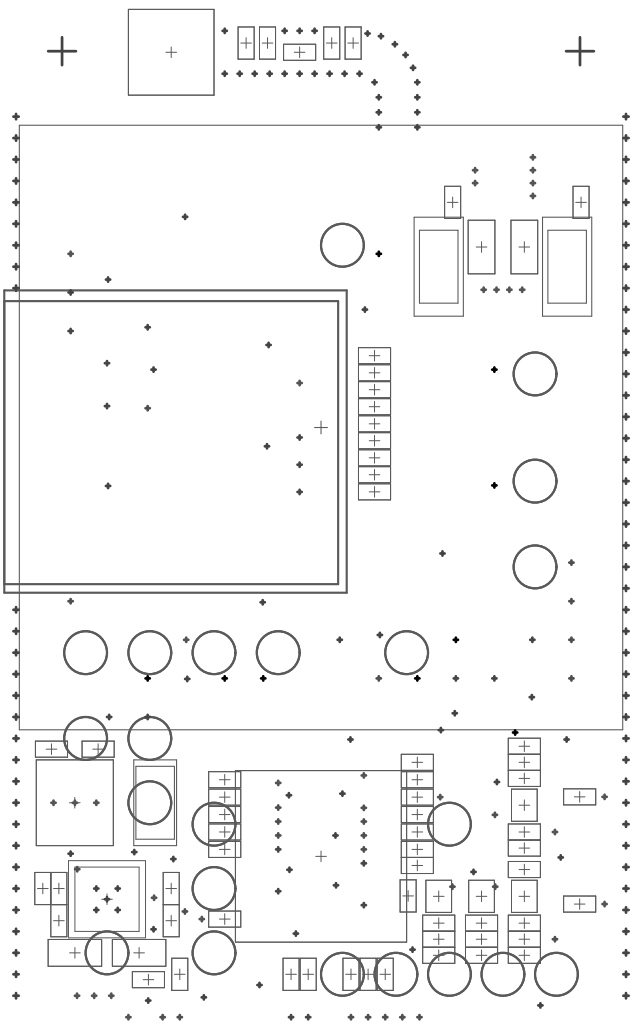
[picture p79: page 2]
