akkoyun/B101/Output/2026-04-23/PCB Print/Solder/Paste Mask Prints.PDF

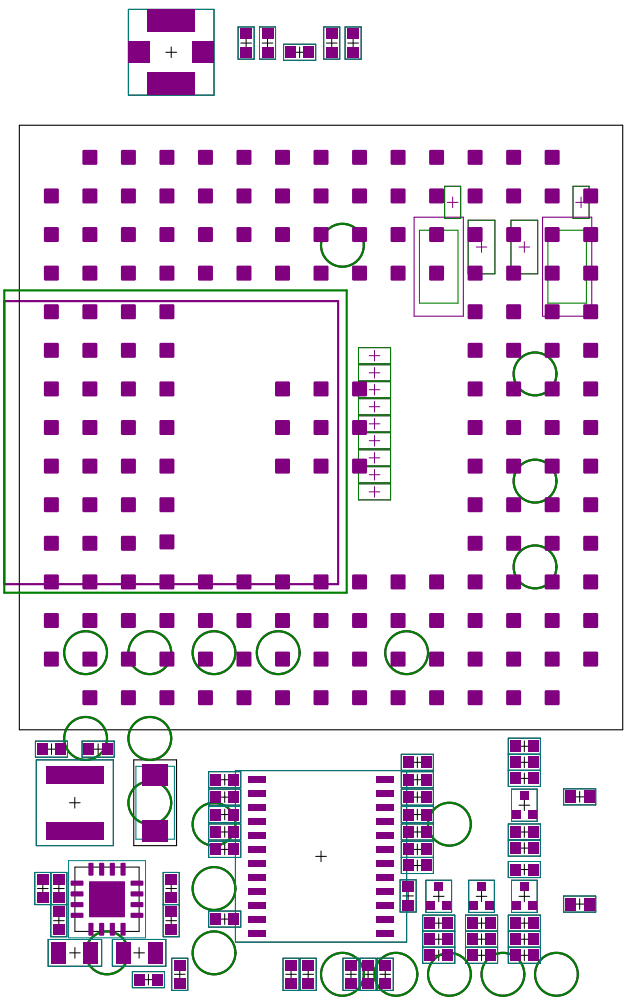
[picture p80: page 1]

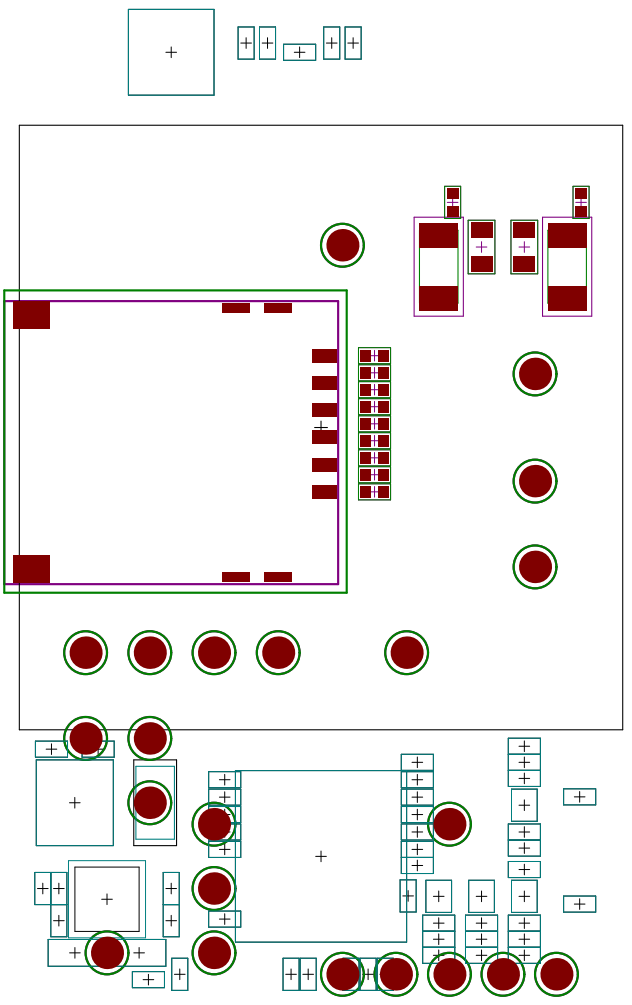
[picture p81: page 2]

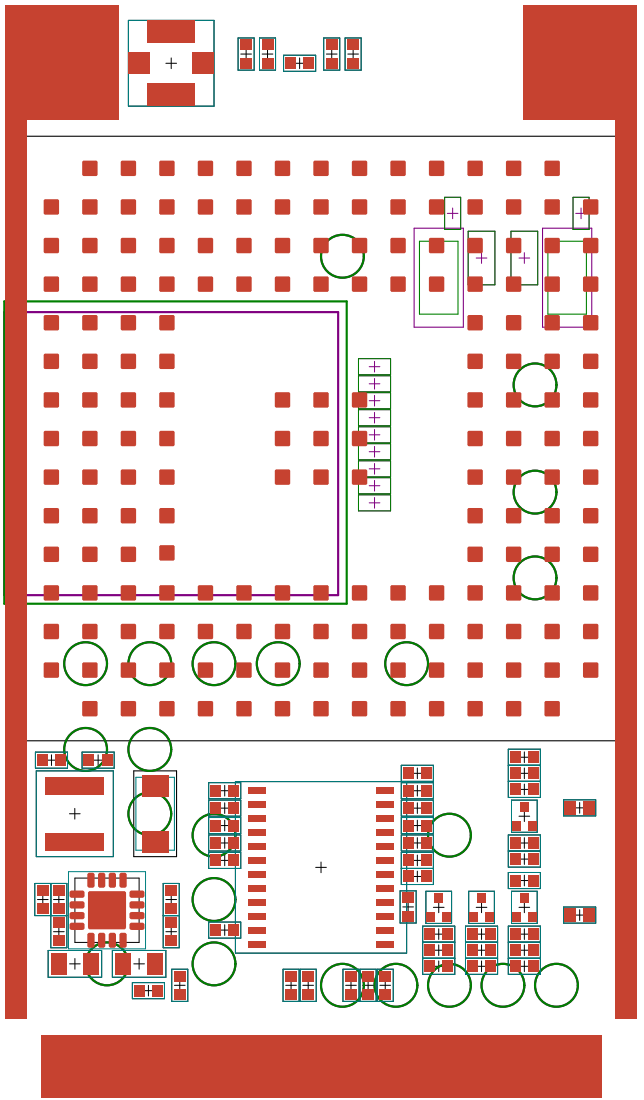
[picture p82: page 3]

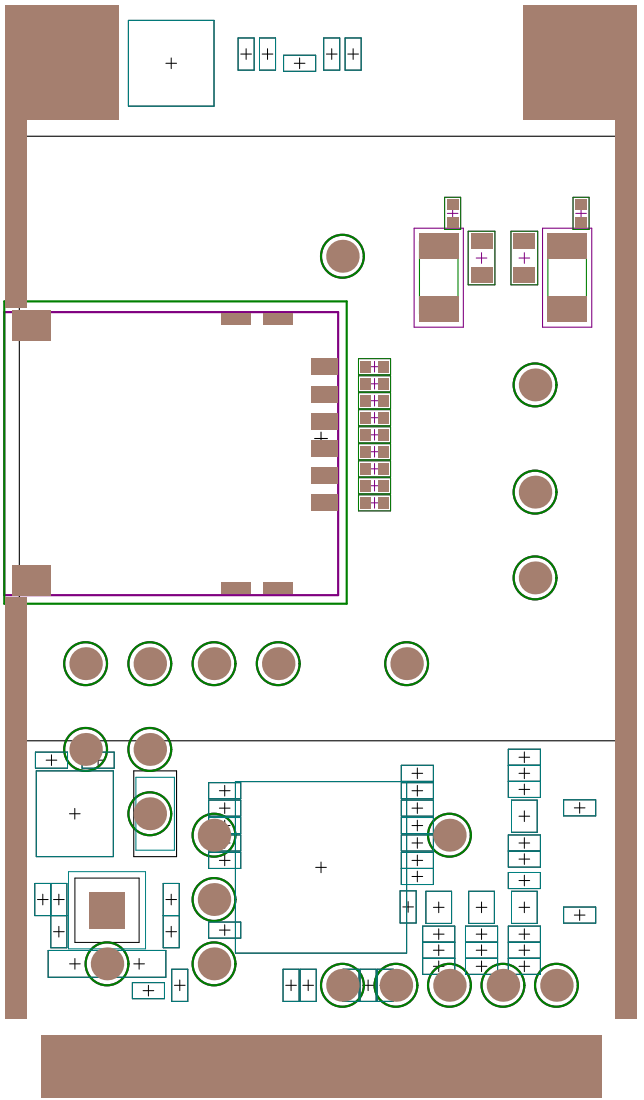
[picture p83: page 4]
