akkoyun/B101/Output/2026-02-26/PCB Print/Drill Drawing/Guides.PDF

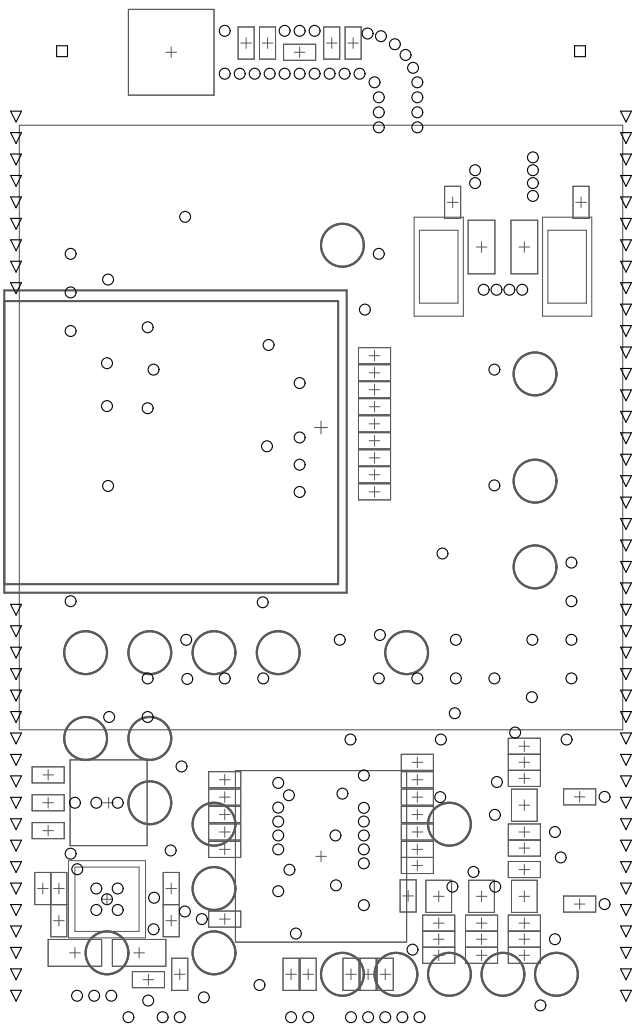
[picture p84: page 1]

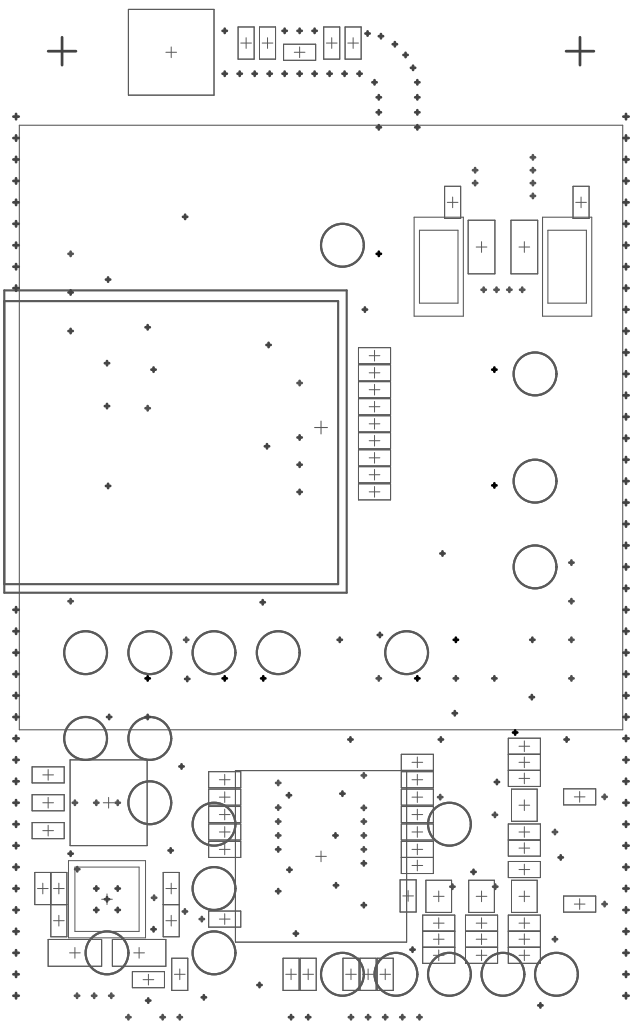
[picture p85: page 2]
