akkoyun/B101/Output/2026-02-26/PCB Print/Solder/Paste Mask Prints.PDF

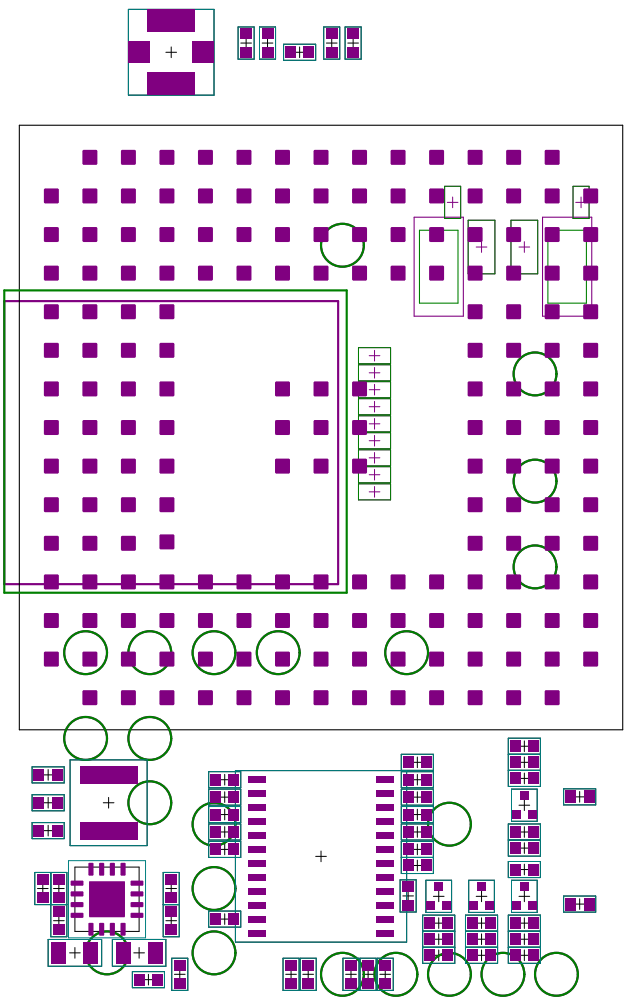
[picture p86: page 1]

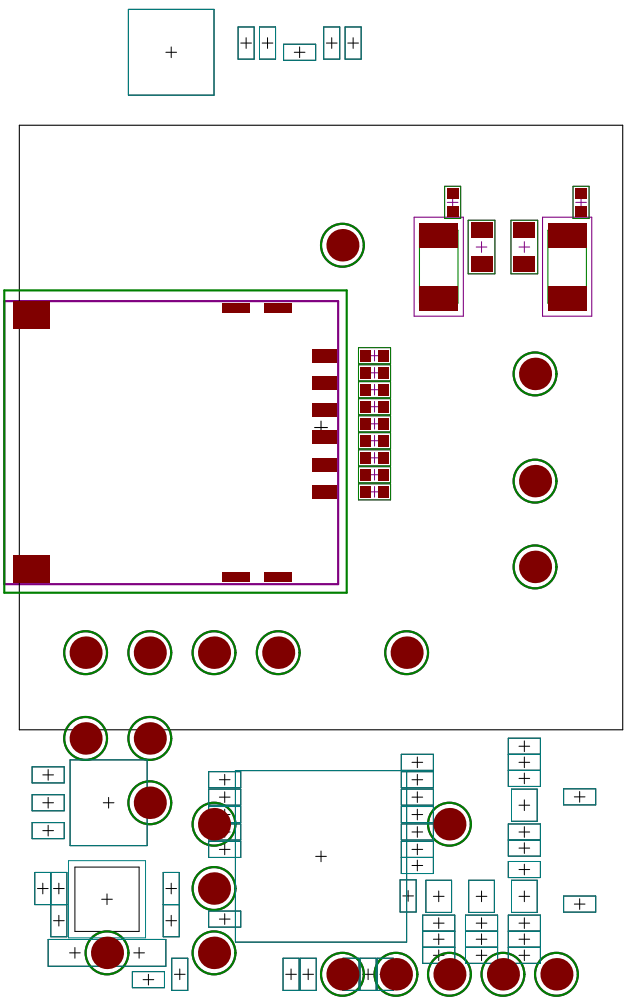
[picture p87: page 2]

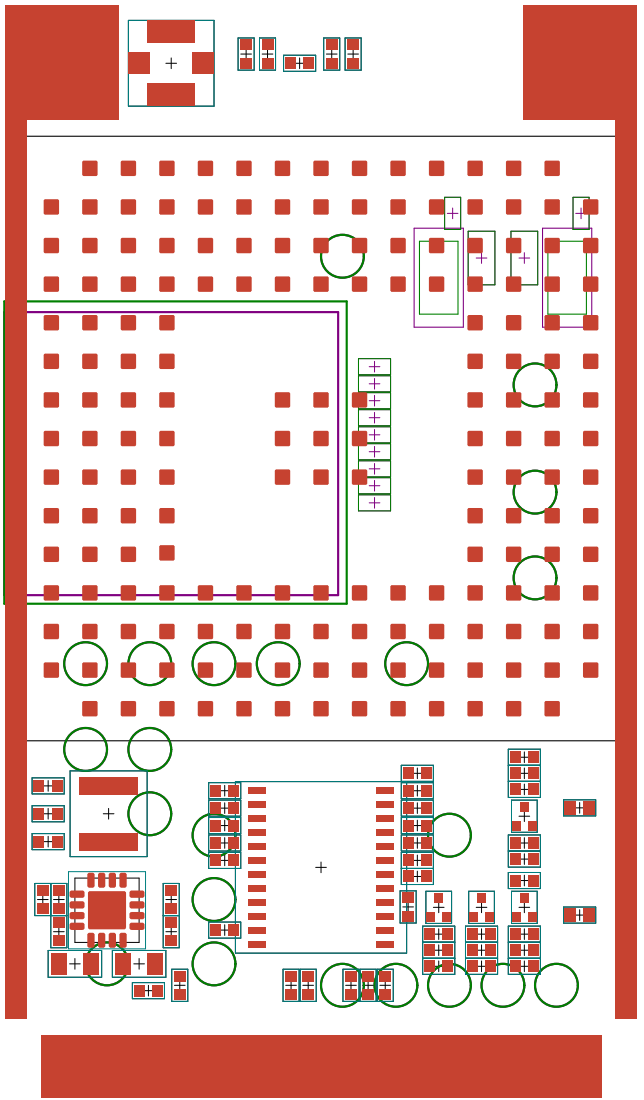
[picture p88: page 3]

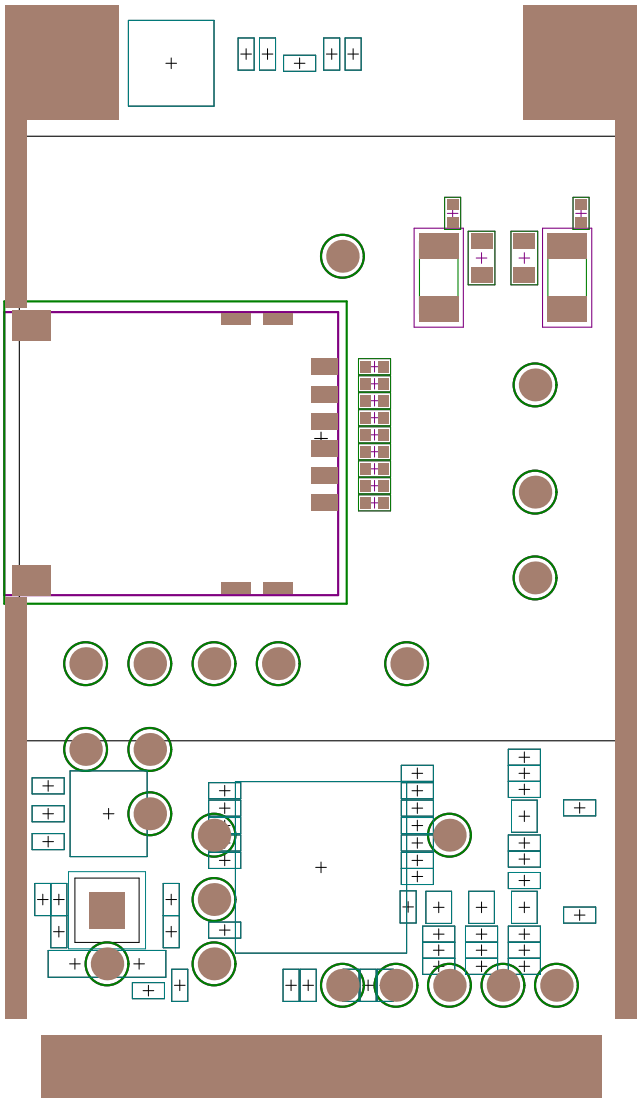
[picture p89: page 4]
