akkoyun/B101/Output/2026-02-18/PCB Print/Drill Drawing/Guides.PDF

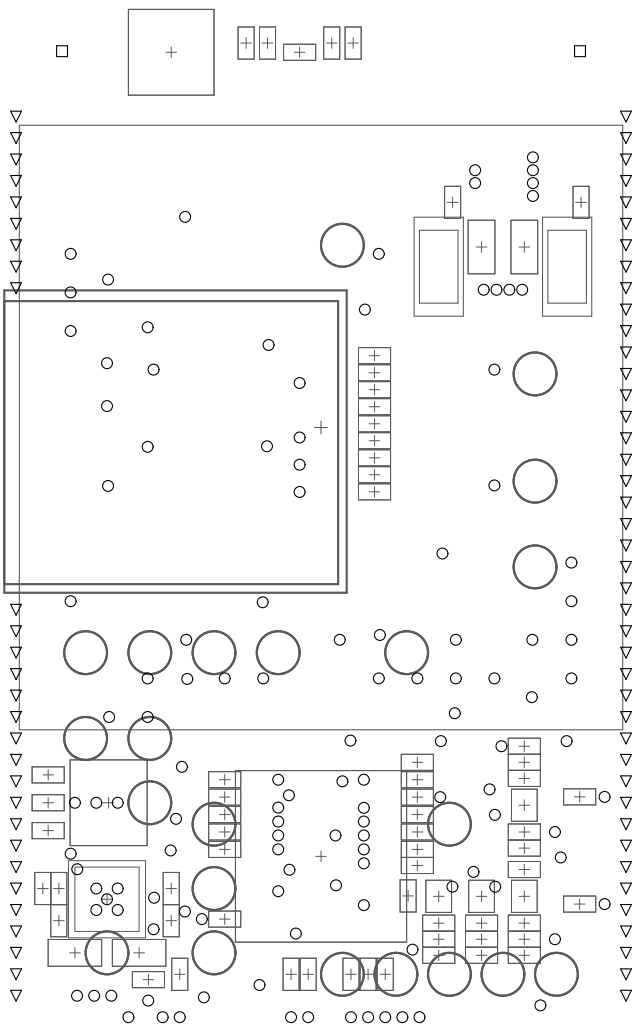
[picture p90: page 1]

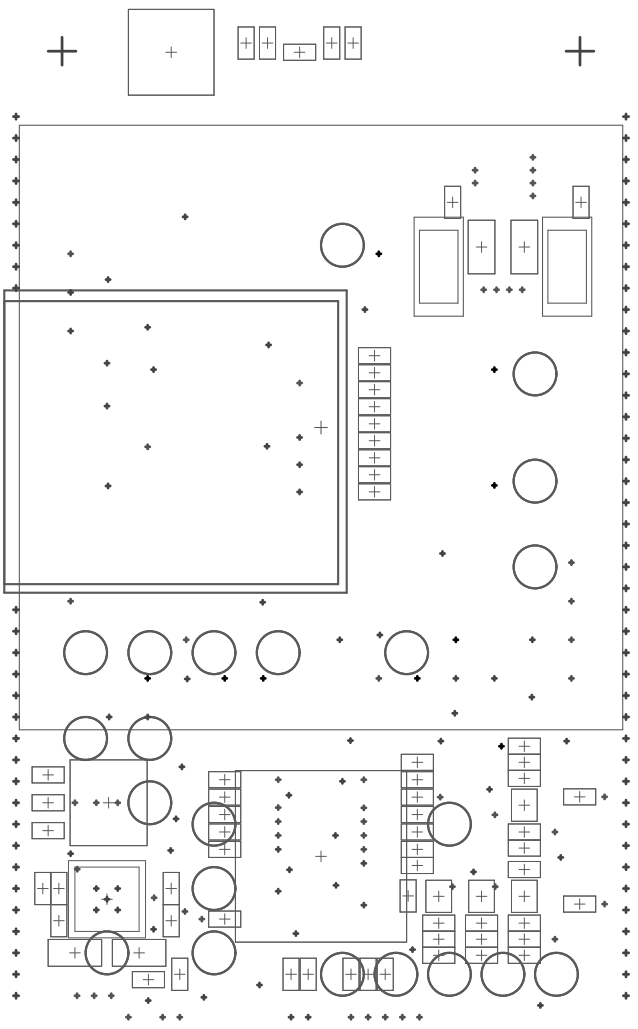
[picture p91: page 2]
