akkoyun/B101/Output/2026-02-18/PCB Print/Solder/Paste Mask Prints.PDF

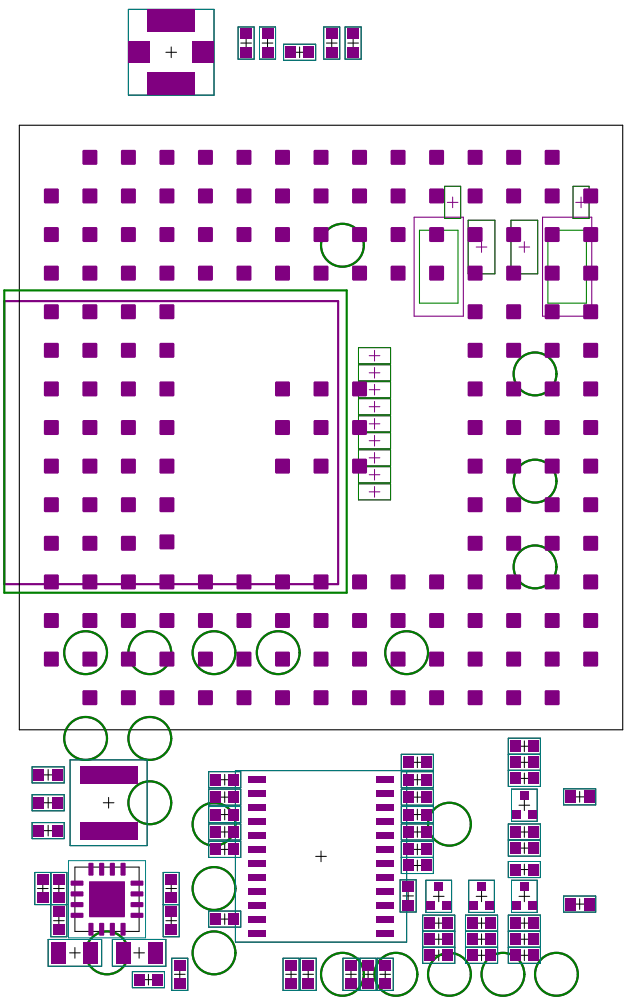
[picture p92: page 1]

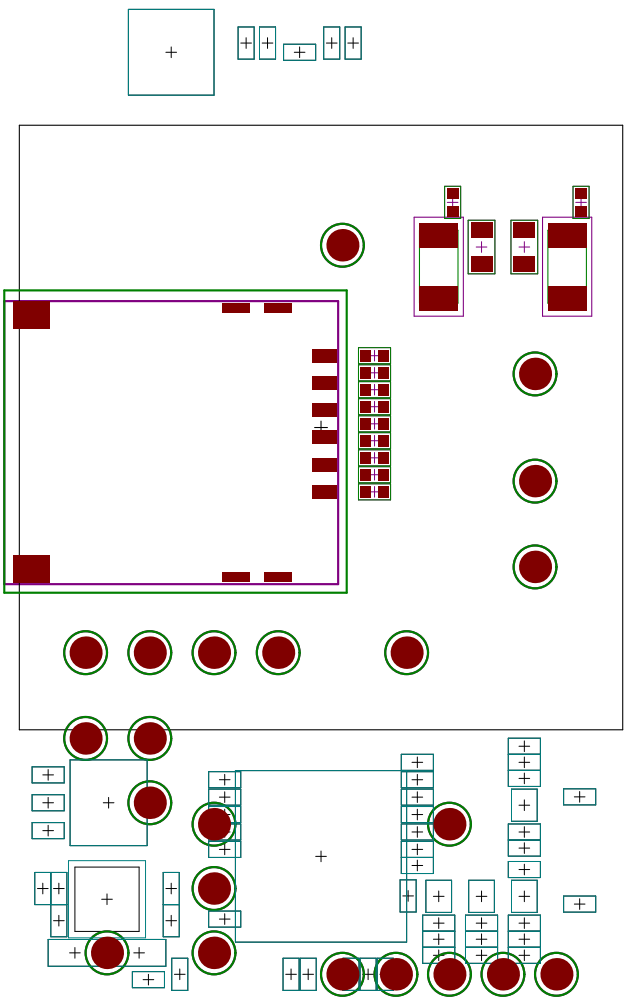
[picture p93: page 2]

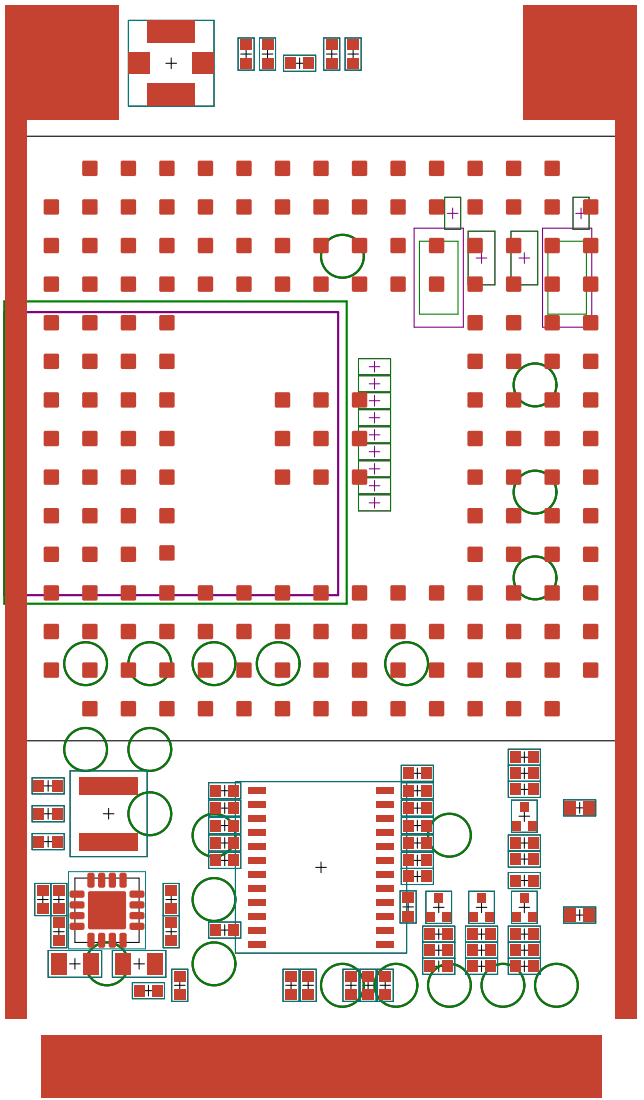
[picture p94: page 3]

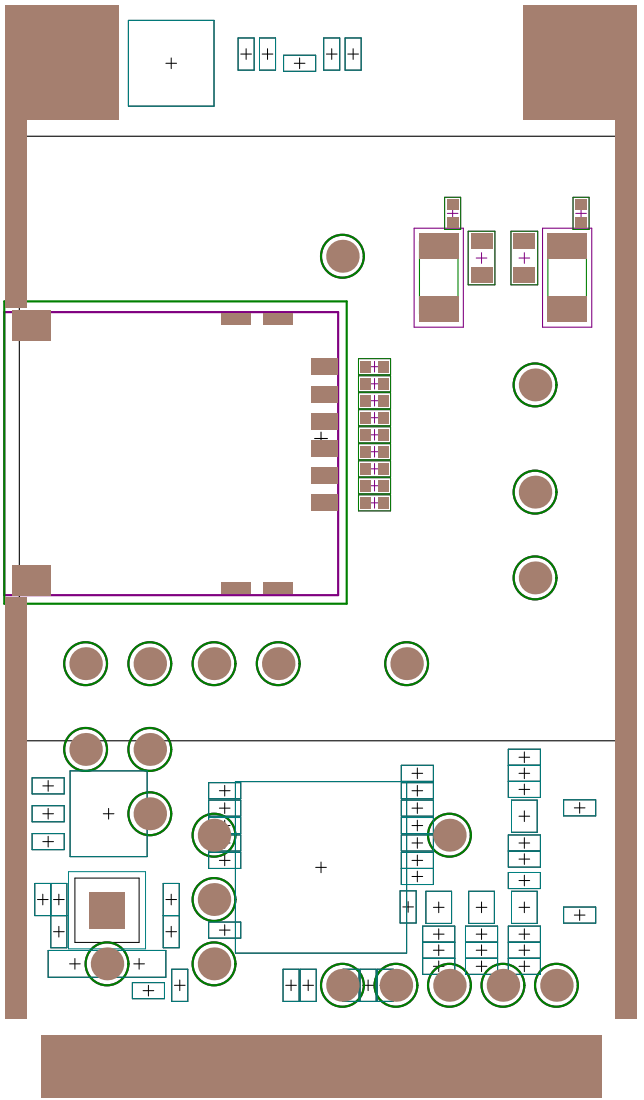
[picture p95: page 4]
