akkoyun/B101/Output/2026-02-18/DRC/Design Rules Check.PDF

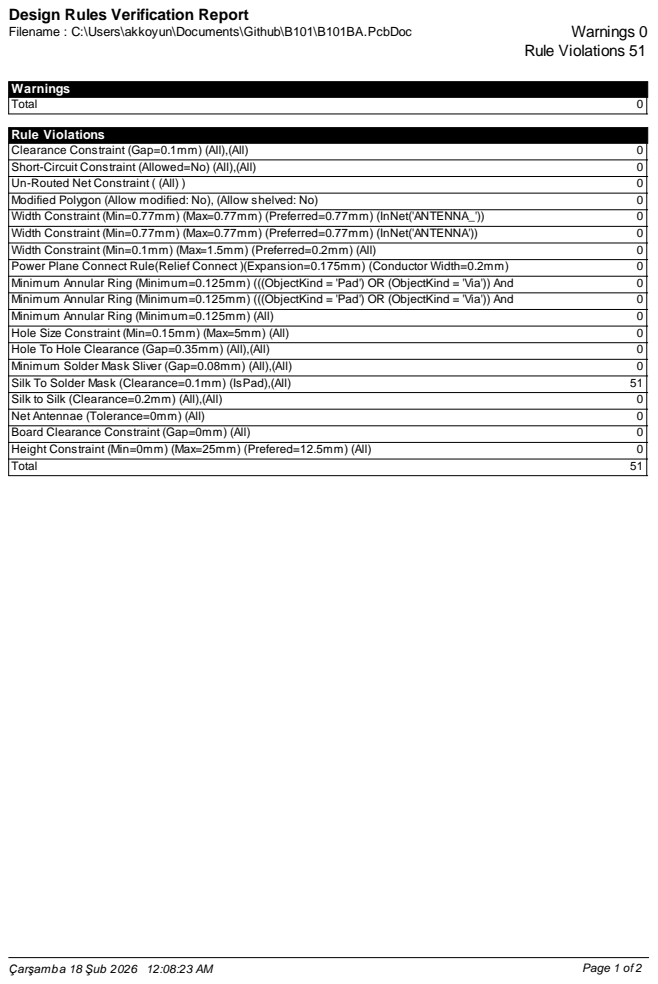
[picture p98: page 1]

Design Rules Verification Report

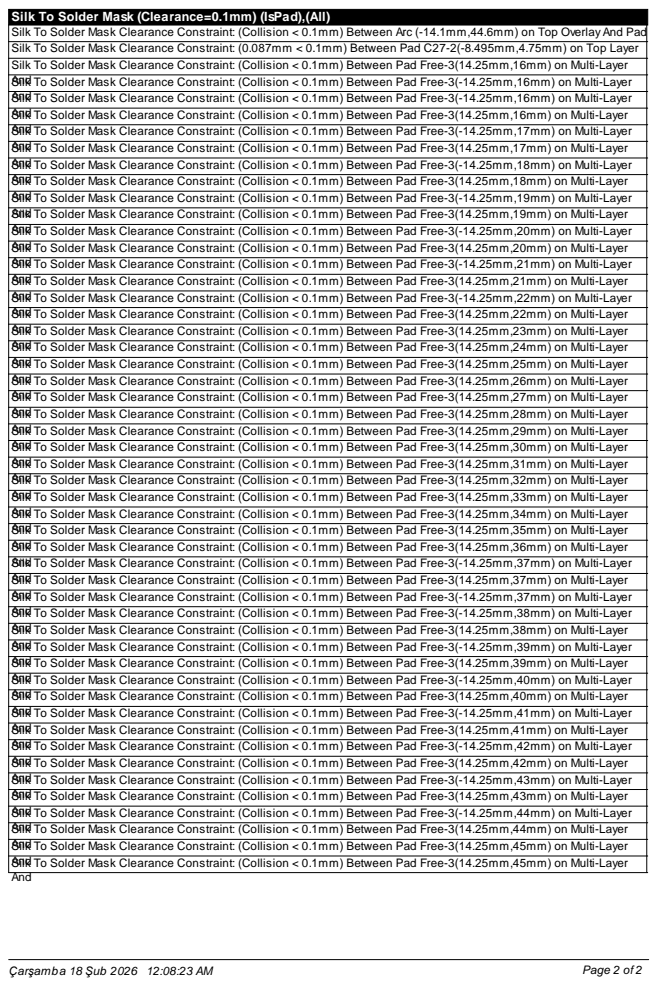
[picture p99: page 2]

Silk To Solder Mask (Clearance=0.1mm) (IsPad),(All)
Silk To Solder Mask Clearance Constraint: (Collision < 0.1mm) Between Arc (-14.1mm,44.6mm) on Top OverlayAnd Pad
Silk To Solder Mask Clearance Constraint: (0.087mm < 0.1mm) Between Pad C27-2(-8.495mm,4.75mm) on Top Layer
Silk To Solder Mask Clearance Constraint: (Collision < 0.1mm) Between Pad Free-3(14.25mm,16mm) on Multi-Layer
ASinldk To Solder Mask Clearance Constraint: (Collision < 0.1mm) Between Pad Free-3(-14.25mm,16mm) on Multi-Layer
ASinldk To Solder Mask Clearance Constraint: (Collision < 0.1mm) Between Pad Free-3(14.25mm,16mm) on Multi-Layer
ASinldk To Solder Mask Clearance Constraint: (Collision < 0.1mm) Between Pad Free-3(-14.25mm,17mm) on Multi-Layer
ASinldk To Solder Mask Clearance Constraint: (Collision < 0.1mm) Between Pad Free-3(14.25mm,17mm) on Multi-Layer
ASinldk To Solder Mask Clearance Constraint: (Collision < 0.1mm) Between Pad Free-3(-14.25mm,18mm) on Multi-Layer
ASinldk To Solder Mask Clearance Constraint: (Collision < 0.1mm) Between Pad Free-3(14.25mm,18mm) on Multi-Layer
ASinldk To Solder Mask Clearance Constraint: (Collision < 0.1mm) Between Pad Free-3(-14.25mm,19mm) on Multi-Layer
ASinldk To Solder Mask Clearance Constraint: (Collision < 0.1mm) Between Pad Free-3(14.25mm,19mm) on Multi-Layer
ASinldk To Solder Mask Clearance Constraint: (Collision < 0.1mm) Between Pad Free-3(-14.25mm,20mm) on Multi-Layer
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
ASinldk To Solder Mask Clearance Constraint: (Collision < 0.1mm) Between Pad Free-3(14.25mm,44mm) on Multi-Layer
ASinldk To Solder Mask Clearance Constraint: (Collision < 0.1mm) Between Pad Free-3(14.25mm,45mm) on Multi-Layer
And
