akkoyun/B101/Output/2026-02-18/PCB 3D Print/PCB 3D Print (Front).PDF

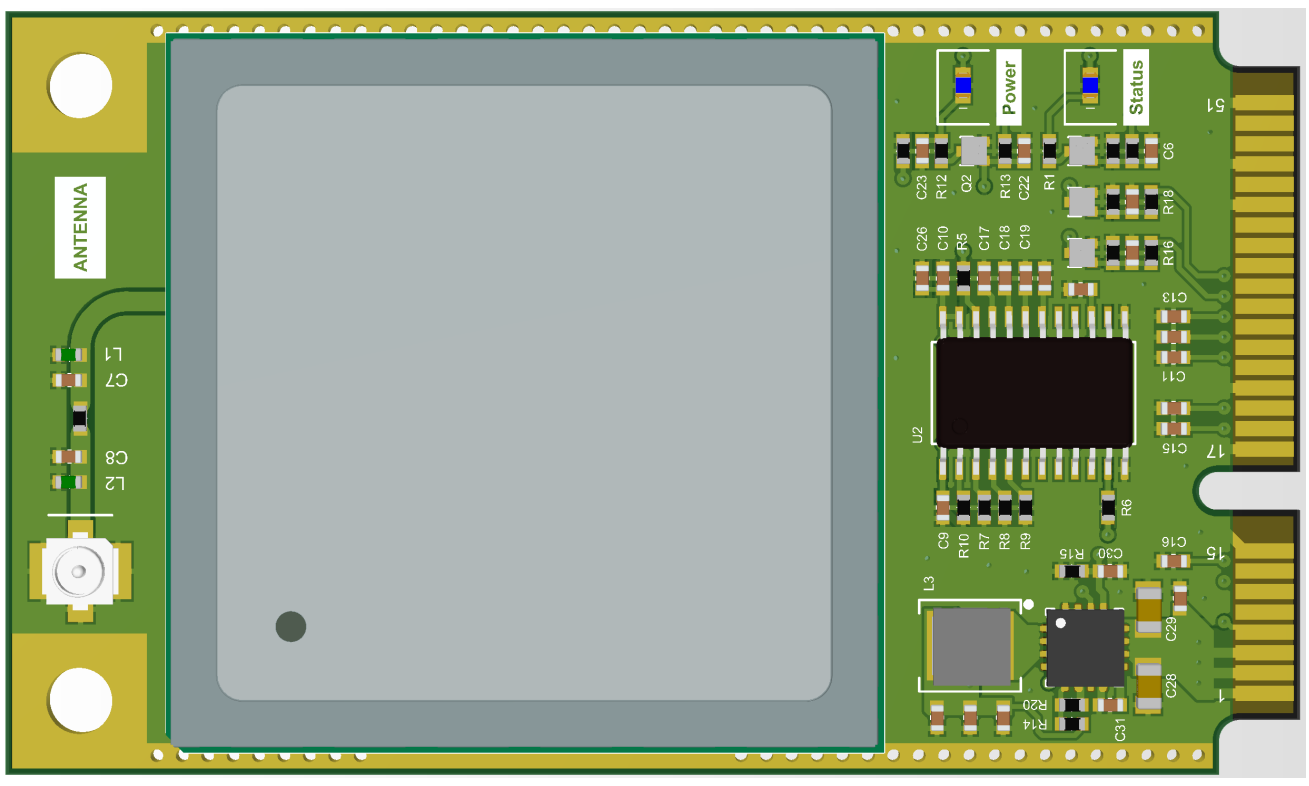
[picture p100: page 1]
