akkoyun/B101/Output/2026-04-23/PCB 3D Print/PCB 3D Print (Back).PDF

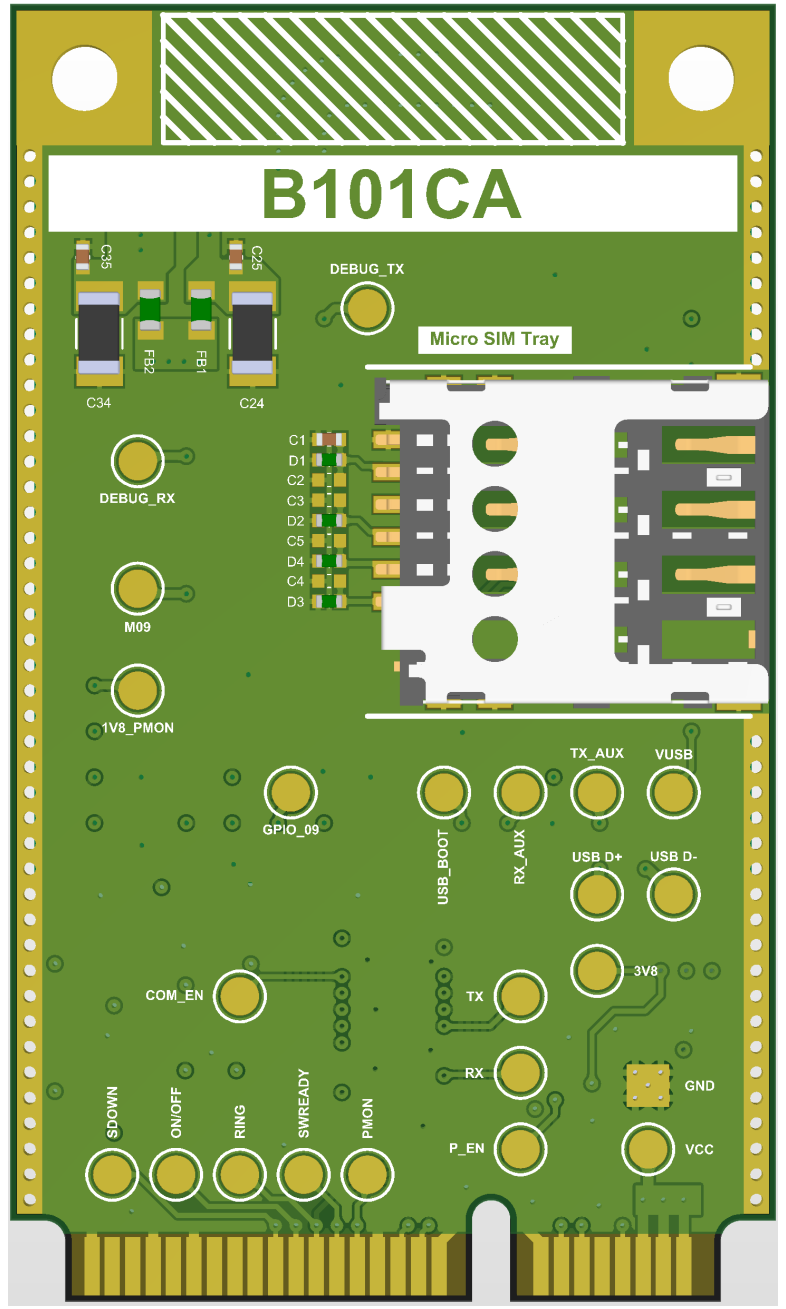
[picture p101: page 1]
