akkoyun/B101/Output/2026-04-23/PCB 3D Print/PCB 3D Print (Front).PDF

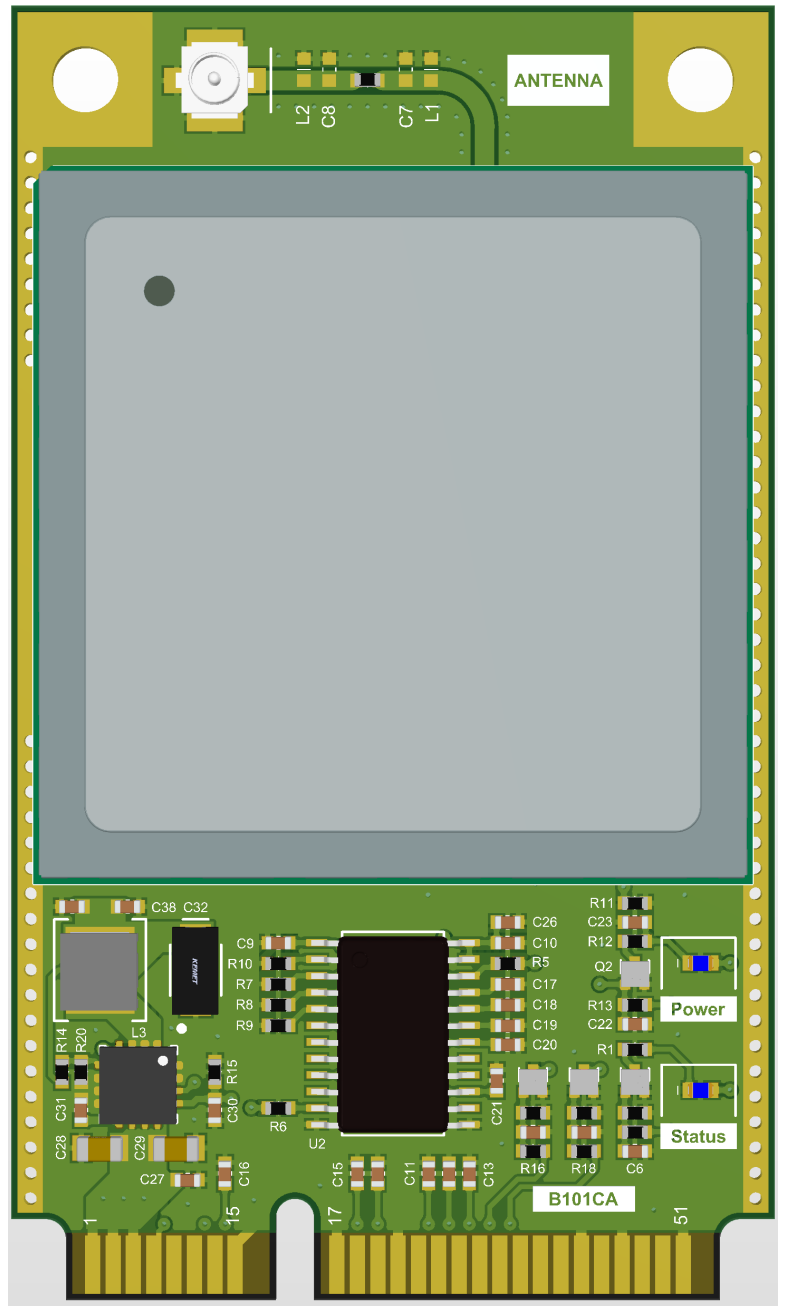
[picture p102: page 1]
