akkoyun/B101/Output/2026-04-23/PCB Print/Assembly Drawings.PDF

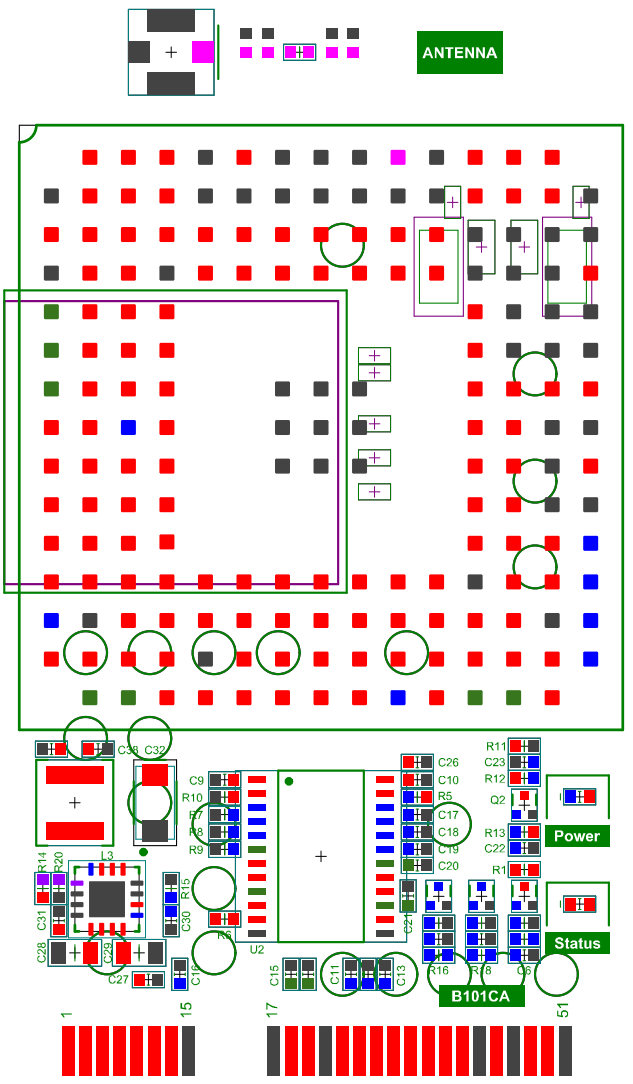
[picture p103: page 1]

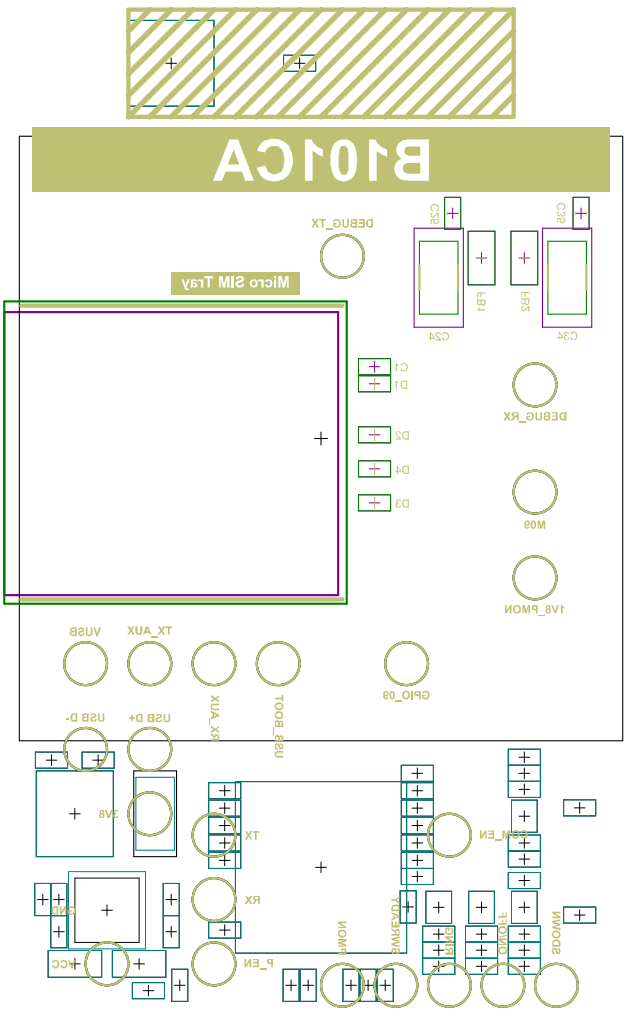
[picture p104: page 2]

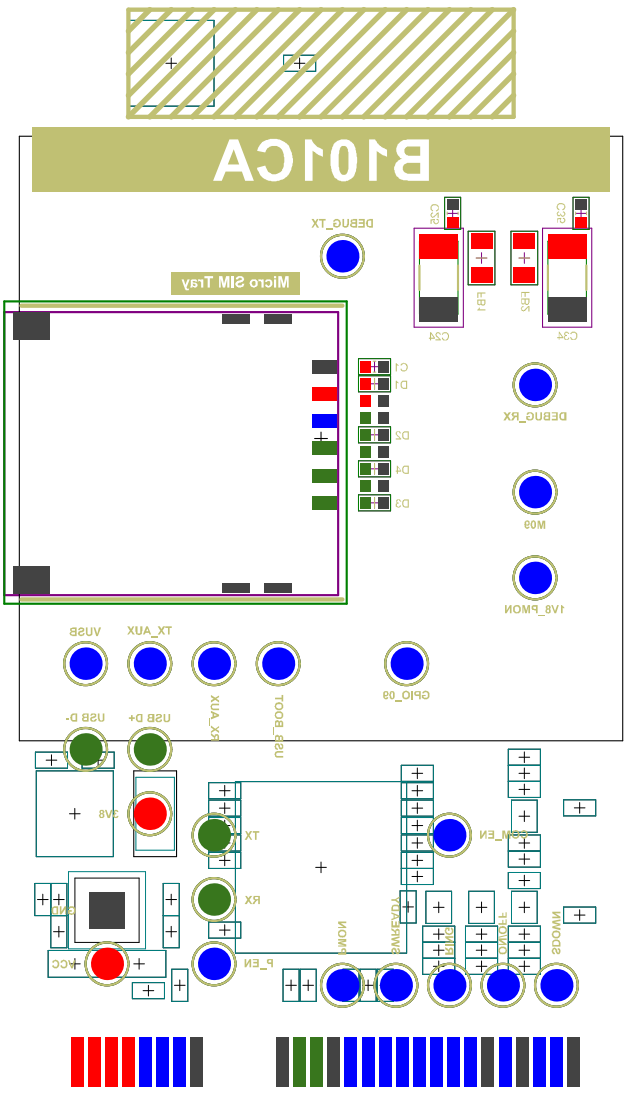
[picture p105: page 4]
