akkoyun/B101/Output/2026-04-23/PCB Print/Composite Drill Drawing.PDF

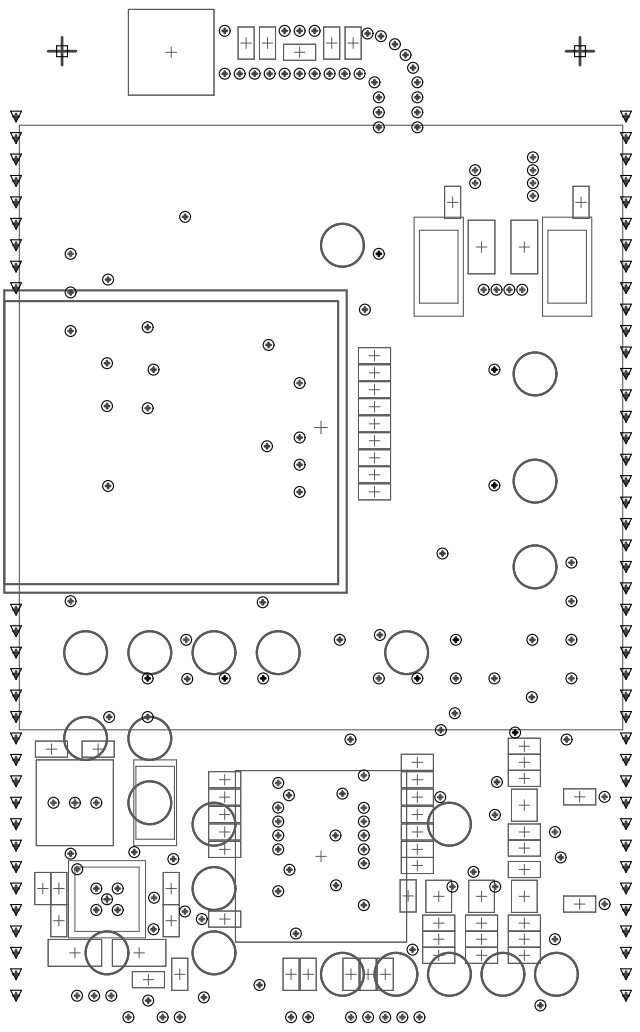
[picture p106: page 1]
