akkoyun/B101/Output/2026-02-26/PCB 3D Print/PCB 3D Print (Back).PDF

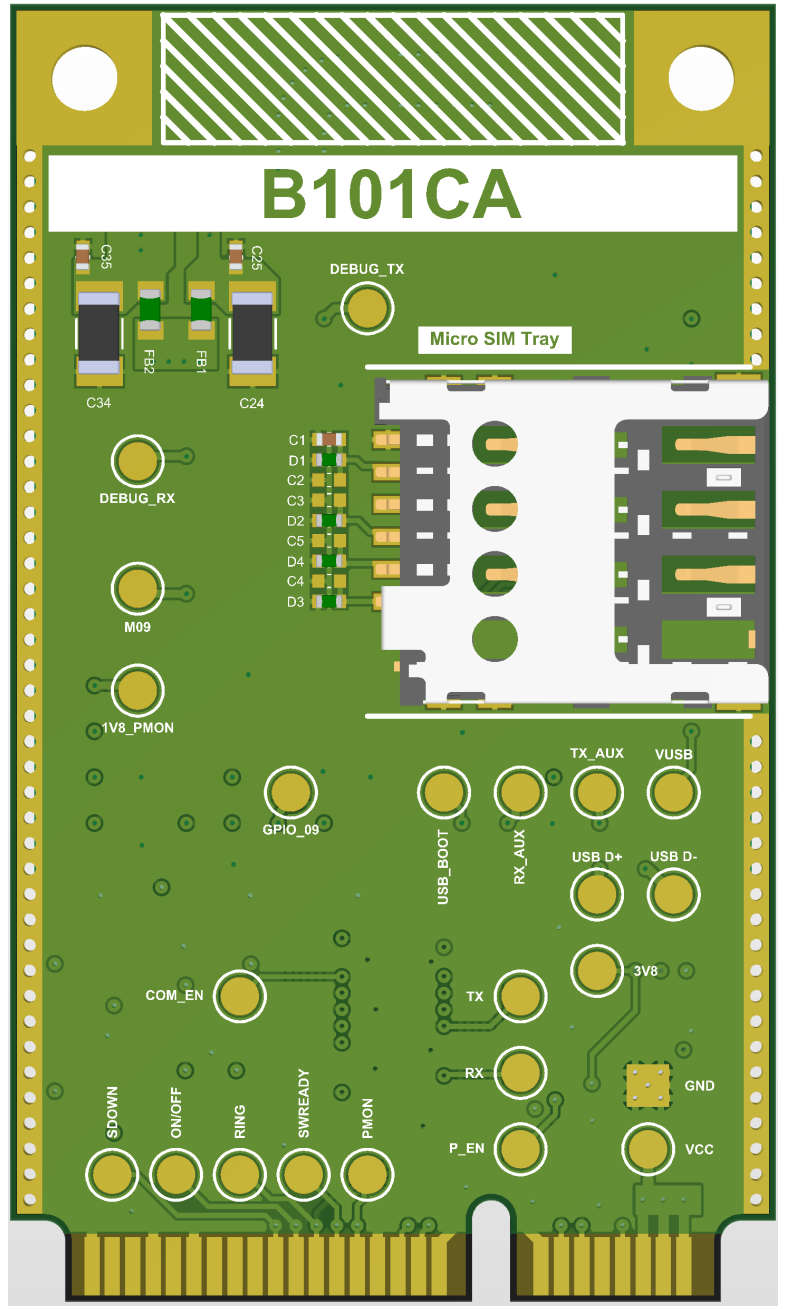
[picture p107: page 1]
