akkoyun/B101/Output/2026-02-26/PCB 3D Print/PCB 3D Print (Front).PDF

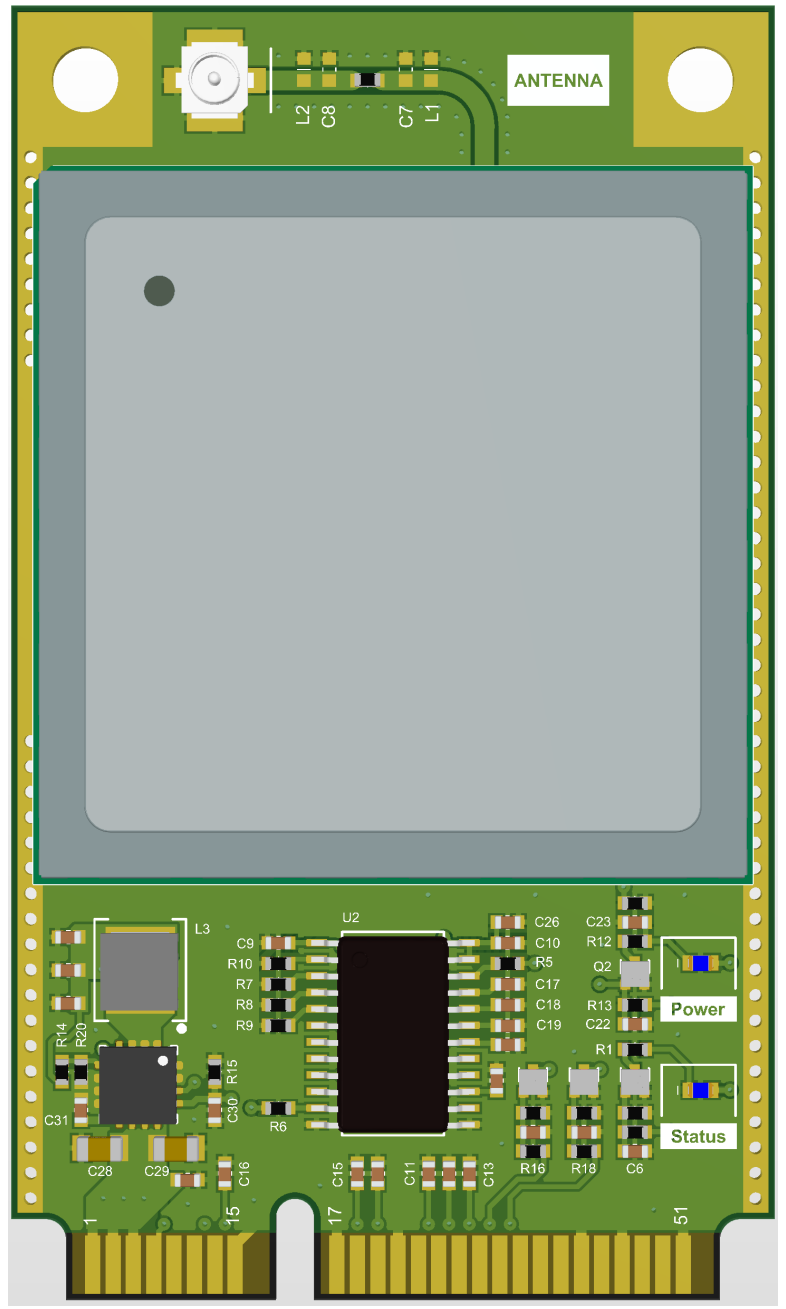
[picture p108: page 1]
