akkoyun/B101/Output/2026-02-26/PCB Print/Assembly Drawings.PDF

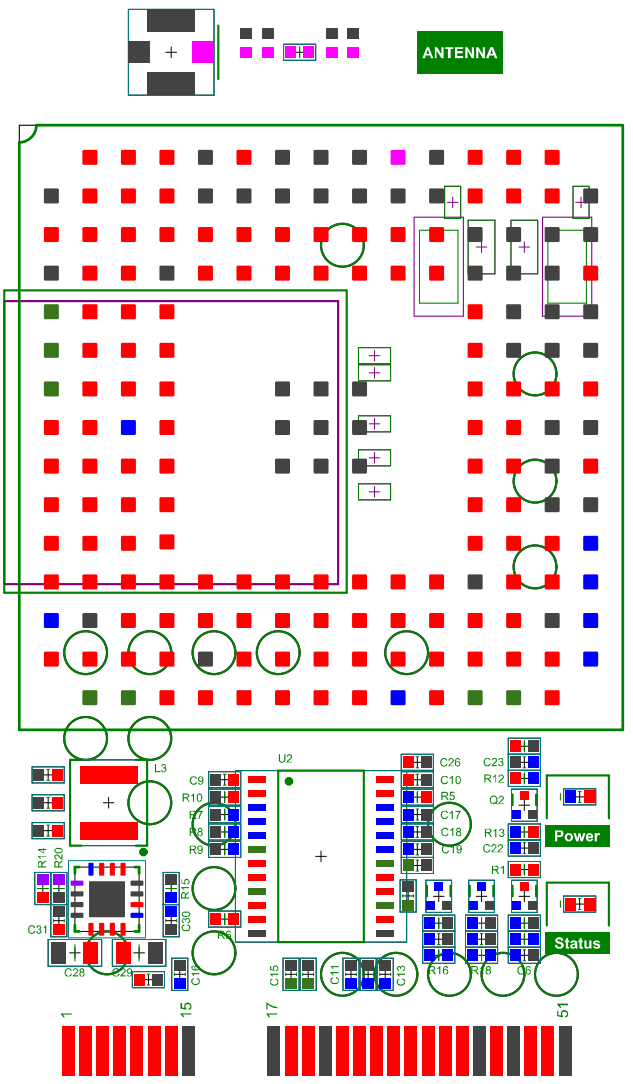
[picture p109: page 1]

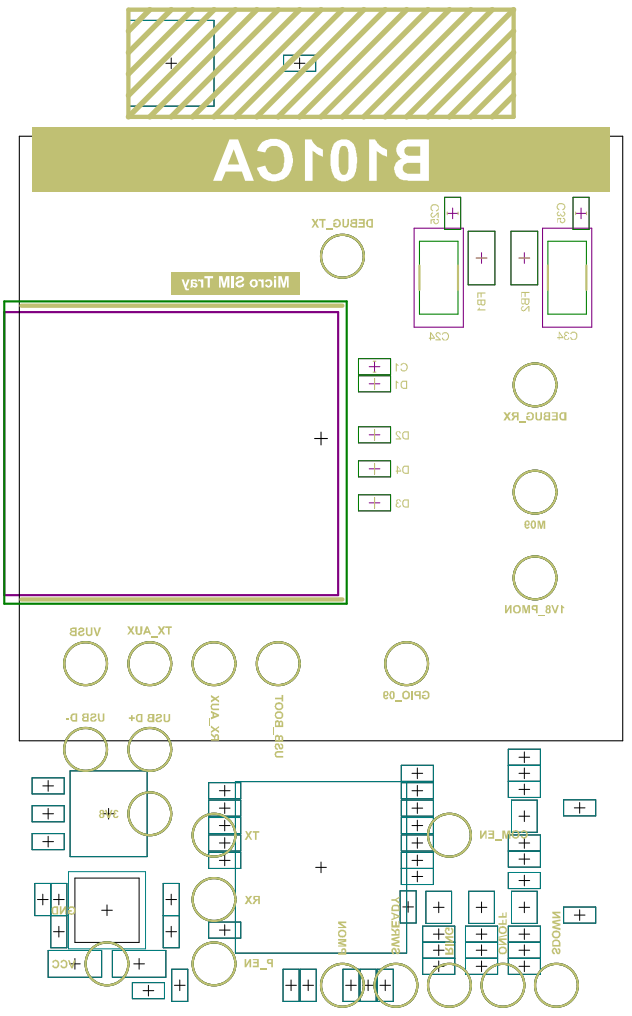
[picture p110: page 2]

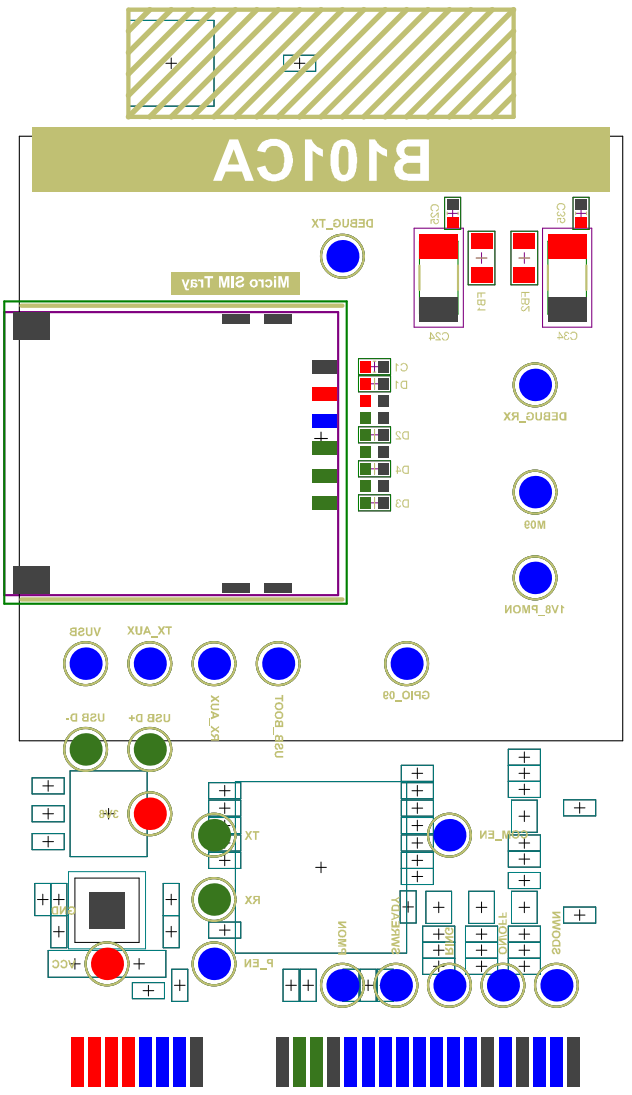
[picture p111: page 4]
