akkoyun/B101/Output/2026-02-26/PCB Print/Composite Drill Drawing.PDF

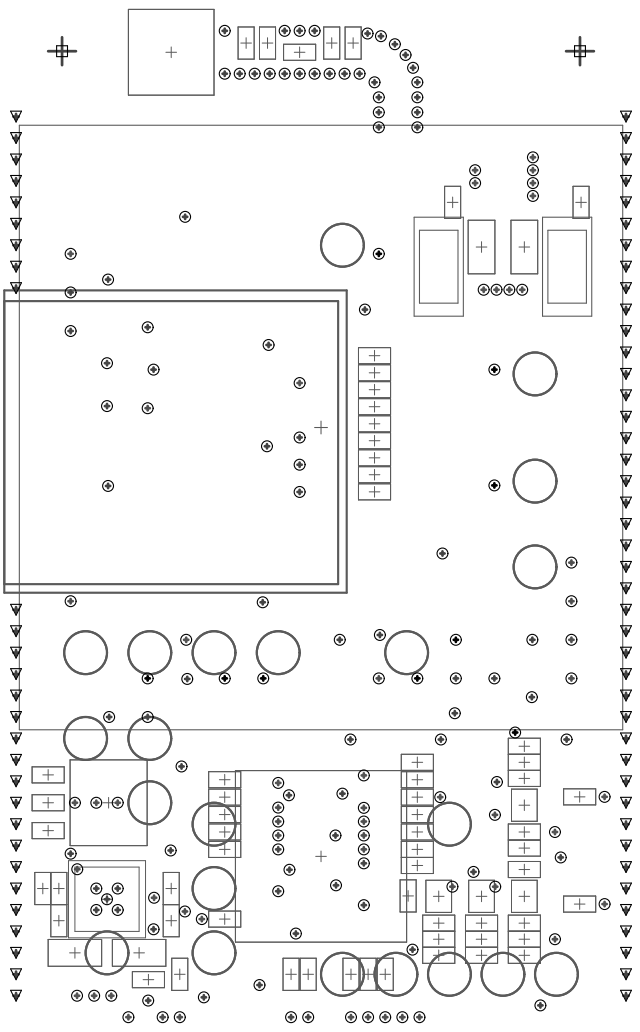
[picture p112: page 1]
