akkoyun/B101/Output/2026-02-18/PCB 3D Print/PCB 3D Print (Back).PDF

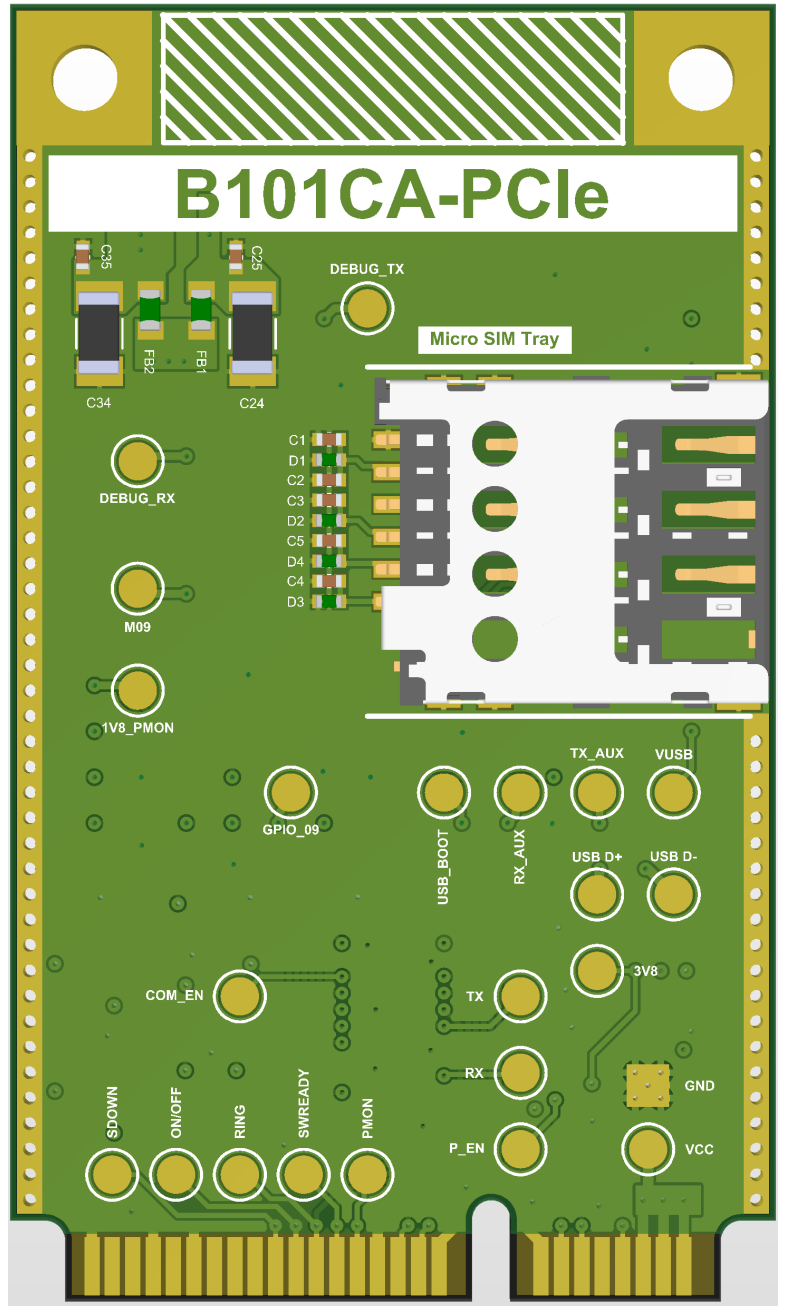
[picture p113: page 1]
