akkoyun/B101/Output/2026-02-18/PCB Print/Assembly Drawings.PDF

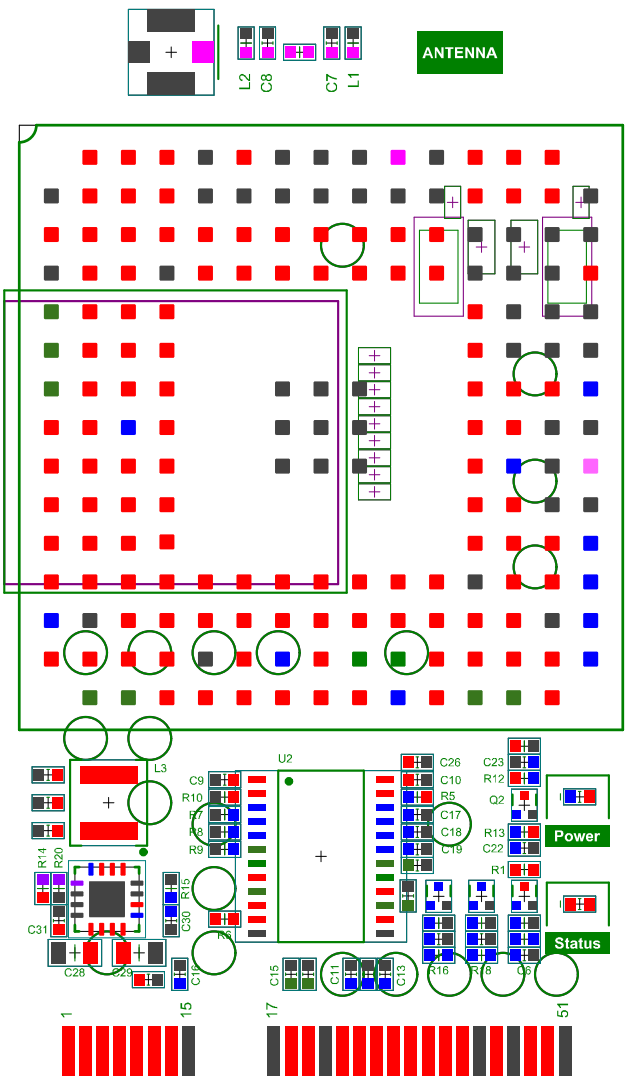
[picture p114: page 1]

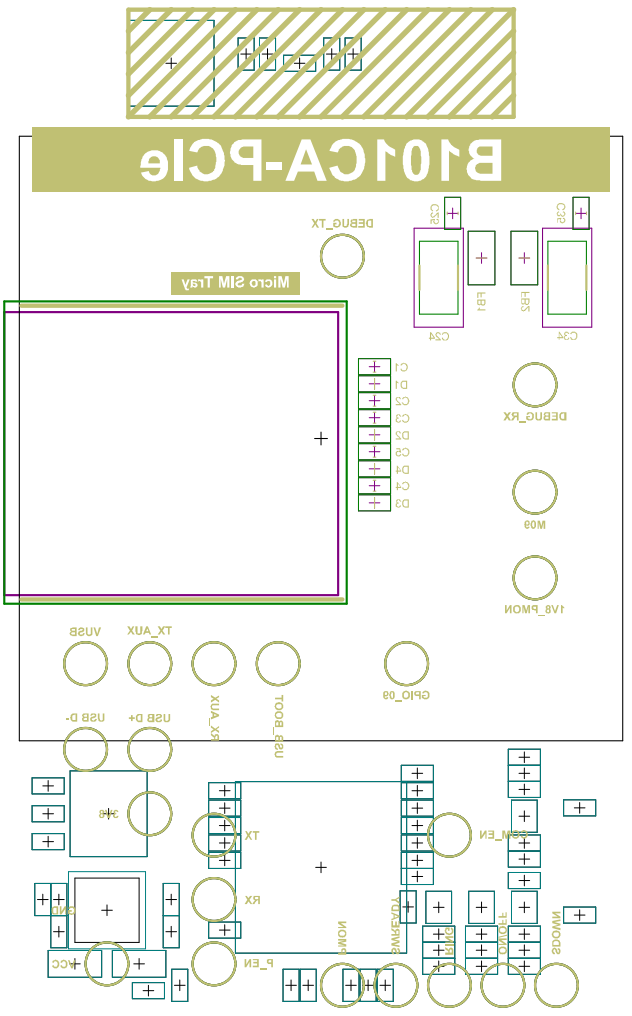
[picture p115: page 2]

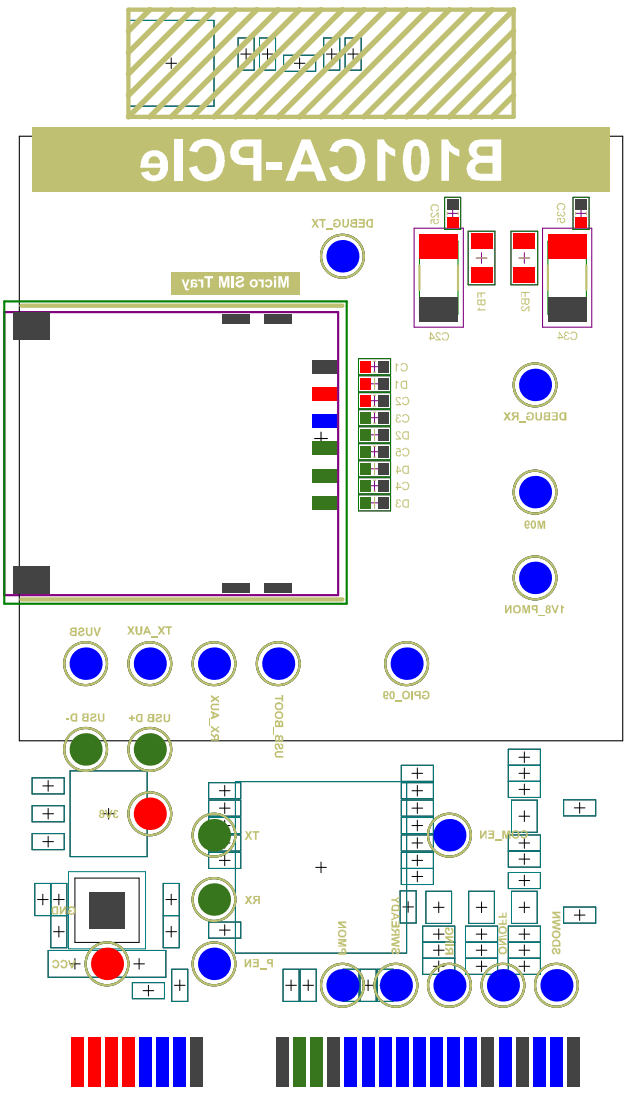
[picture p116: page 4]
