akkoyun/B101/Output/2026-02-18/PCB Print/Composite Drill Drawing.PDF

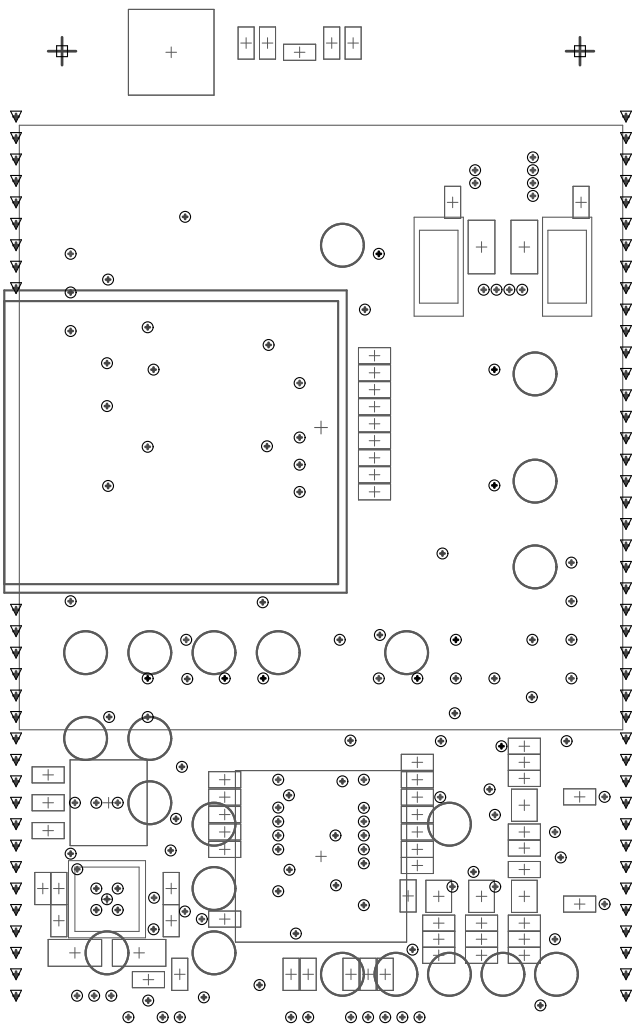
[picture p117: page 1]
